ArthurLimaMiranda/Projeto_FigurePicker/Recursos/simulacao.png

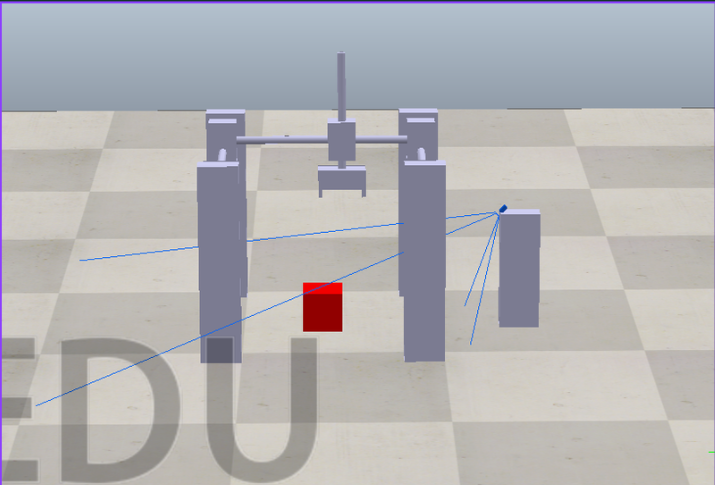
Recursos/simulacao.png
