ArthurLimaMiranda/Projeto_FigurePicker/Vision_picker/yolov11s/runs/detect/cubes_spheres_yolo11s/BoxPR_curve.png

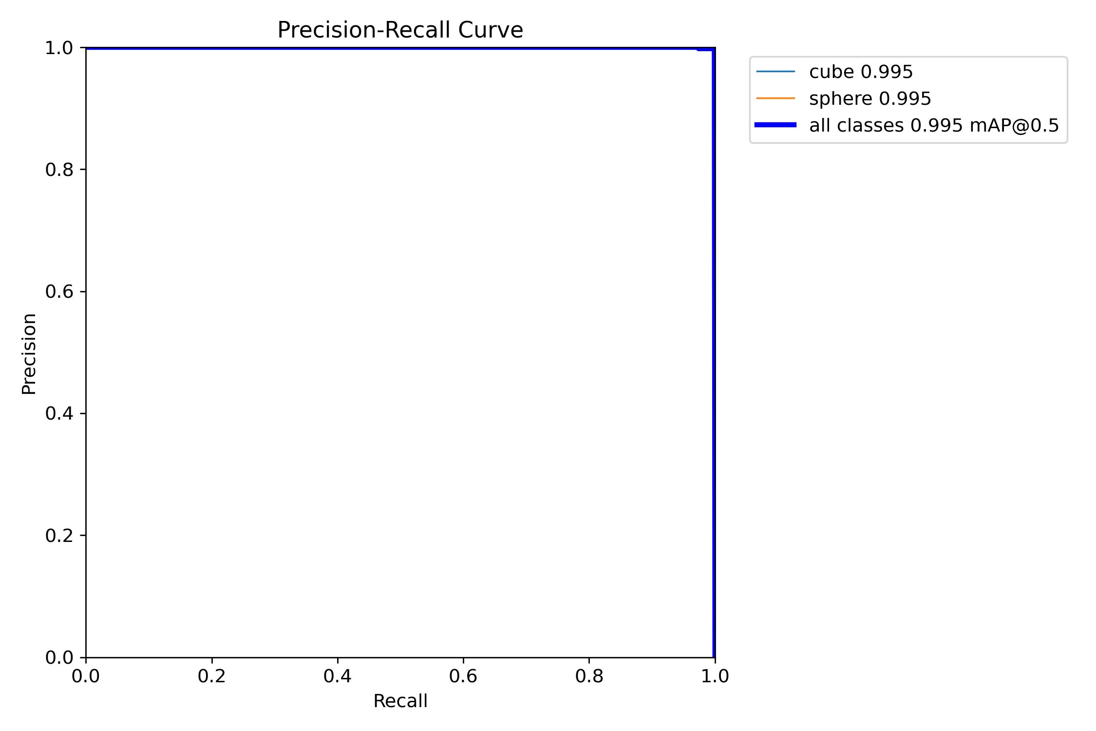
Vision_picker/yolov11s/runs/detect/cubes_spheres_yolo11s/BoxPR_curve.png
