ArthurLimaMiranda/Projeto_FigurePicker/Vision_picker/yolov11s/runs/detect/cubes_spheres_yolo11s/confusion_matrix_normalized.png

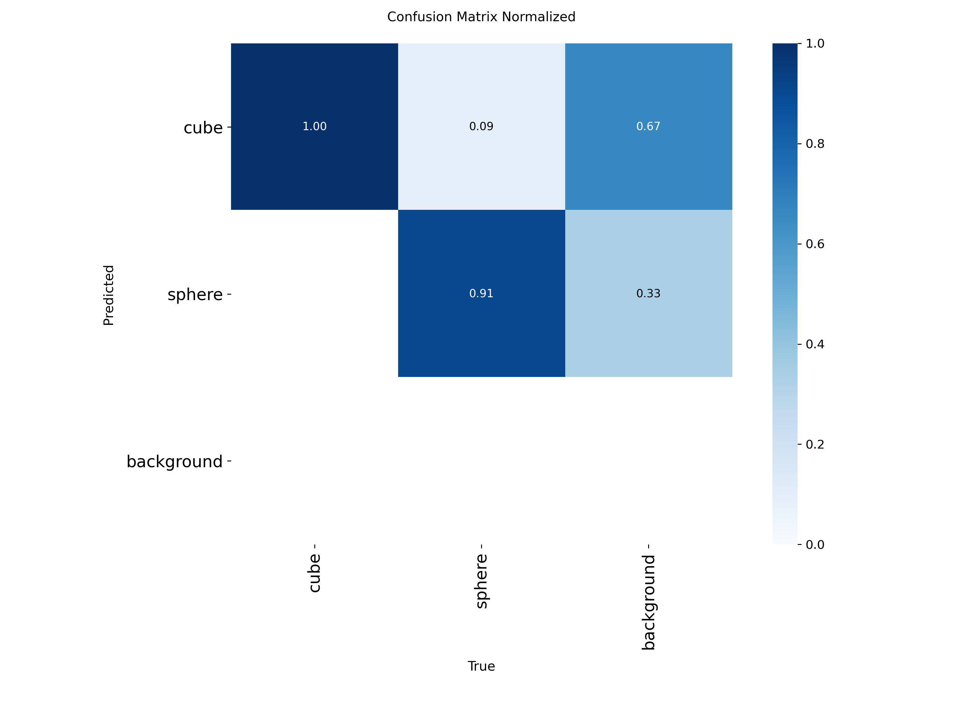
Vision_picker/yolov11s/runs/detect/cubes_spheres_yolo11s/confusion_matrix_normalized.png
