ArthurLimaMiranda/Projeto_FigurePicker/Vision_picker/yolov11s/runs/detect/cubes_spheres_yolo11s/train_batch14141.jpg

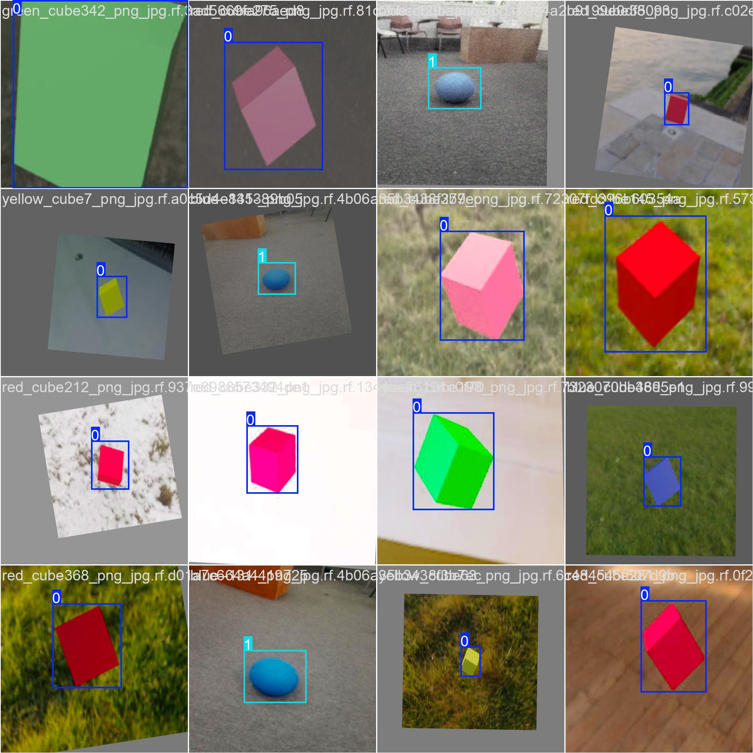
Vision_picker/yolov11s/runs/detect/cubes_spheres_yolo11s/train_batch14141.jpg
