ArthurLimaMiranda/Projeto_FigurePicker/Vision_picker/yolov11s/runs/detect/cubes_spheres_yolo11s/val_batch2_labels.jpg

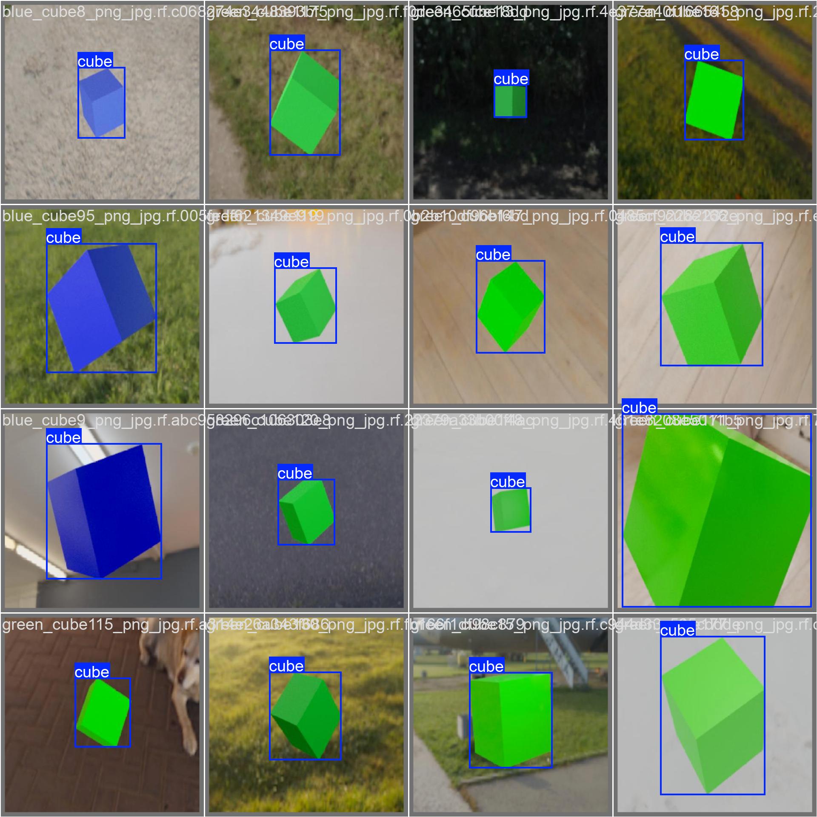
Vision_picker/yolov11s/runs/detect/cubes_spheres_yolo11s/val_batch2_labels.jpg
