ArthurLimaMiranda/Projeto_FigurePicker/Vision_picker/yolov11s/dataset_balanced/test/images/blue--84-_png_jpg.rf.567f411e10d59bb02a4530c11f7e49aa.jpg

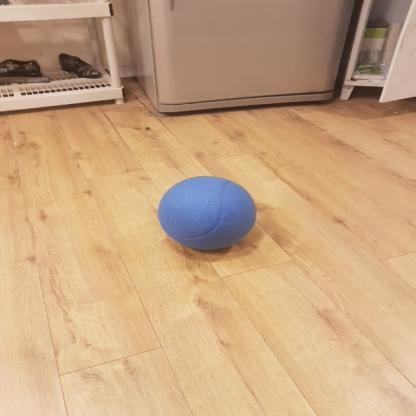
Vision_picker/yolov11s/dataset_balanced/test/images/blue--84-_png_jpg.rf.567f411e10d59bb02a4530c11f7e49aa.jpg
