ArthurLimaMiranda/Projeto_FigurePicker/Vision_picker/yolov11s/dataset_balanced/test/images/blue--93-_png_jpg.rf.6b6eae68098328bdba1f4563f4113ef7.jpg

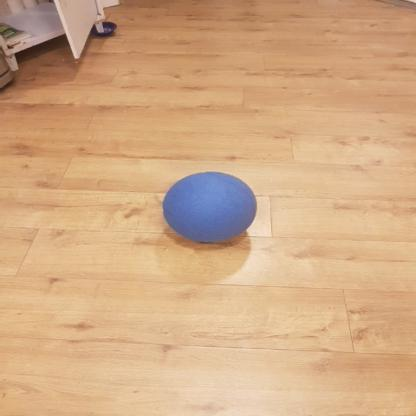
Vision_picker/yolov11s/dataset_balanced/test/images/blue--93-_png_jpg.rf.6b6eae68098328bdba1f4563f4113ef7.jpg
