ArthurLimaMiranda/Projeto_FigurePicker/Vision_picker/yolov11s/dataset_balanced/test/images/blue--100-_png_jpg.rf.dd0b86e63040361fdaaacd52fe4bce31.jpg

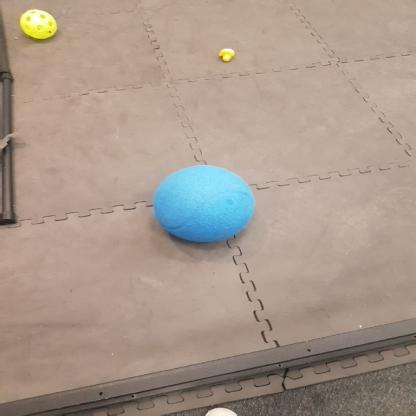
Vision_picker/yolov11s/dataset_balanced/test/images/blue--100-_png_jpg.rf.dd0b86e63040361fdaaacd52fe4bce31.jpg
