ArthurLimaMiranda/Projeto_FigurePicker/Vision_picker/yolov11s/dataset_balanced/test/images/blue_cube42_png_jpg.rf.abce69a664ab6f5cebc19ef82301c86c.jpg

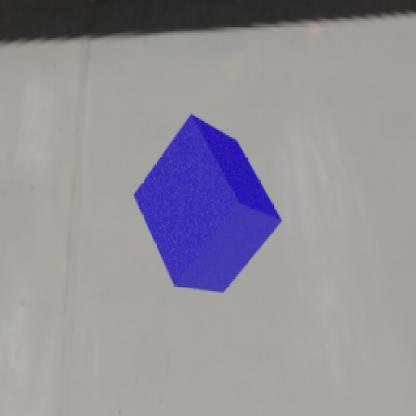
Vision_picker/yolov11s/dataset_balanced/test/images/blue_cube42_png_jpg.rf.abce69a664ab6f5cebc19ef82301c86c.jpg
