ArthurLimaMiranda/Projeto_FigurePicker/Vision_picker/yolov11s/dataset_balanced/test/images/blue_cube58_png_jpg.rf.53a362439758e62a2edbe77619f49d31.jpg

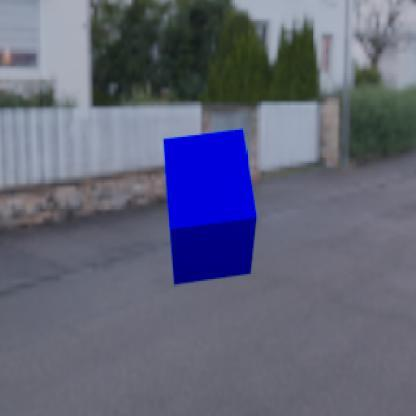
Vision_picker/yolov11s/dataset_balanced/test/images/blue_cube58_png_jpg.rf.53a362439758e62a2edbe77619f49d31.jpg
