ArthurLimaMiranda/Projeto_FigurePicker/Vision_picker/yolov11s/dataset_balanced/test/images/blue_cube85_png_jpg.rf.f3a1650c1c1776d2e01093200efaac4e.jpg

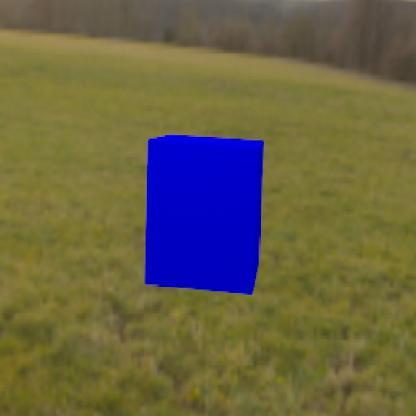
Vision_picker/yolov11s/dataset_balanced/test/images/blue_cube85_png_jpg.rf.f3a1650c1c1776d2e01093200efaac4e.jpg
