ArthurLimaMiranda/Projeto_FigurePicker/Vision_picker/yolov11s/dataset_balanced/test/images/blue_cube103_png_jpg.rf.4e462e84350769a530bda1f3ba2a9905.jpg

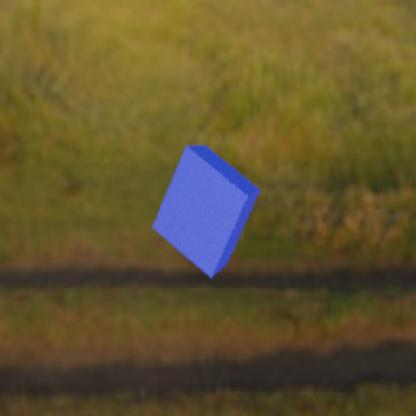
Vision_picker/yolov11s/dataset_balanced/test/images/blue_cube103_png_jpg.rf.4e462e84350769a530bda1f3ba2a9905.jpg
