ArthurLimaMiranda/Projeto_FigurePicker/Vision_picker/yolov11s/dataset_balanced/test/images/blue_cube160_png_jpg.rf.a1abcd2abb369dd8cf45045a25f46531.jpg

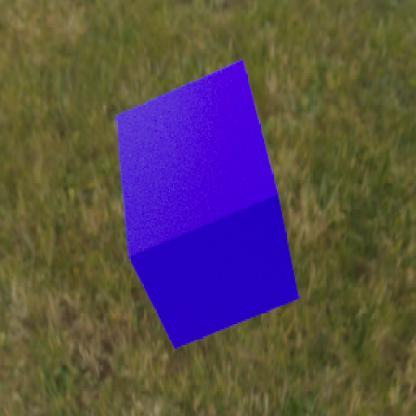
Vision_picker/yolov11s/dataset_balanced/test/images/blue_cube160_png_jpg.rf.a1abcd2abb369dd8cf45045a25f46531.jpg
