ArthurLimaMiranda/Projeto_FigurePicker/Vision_picker/yolov11s/dataset_balanced/test/images/blue_cube161_png_jpg.rf.b45ab2bd1b514e909079901d2c2f8d05.jpg

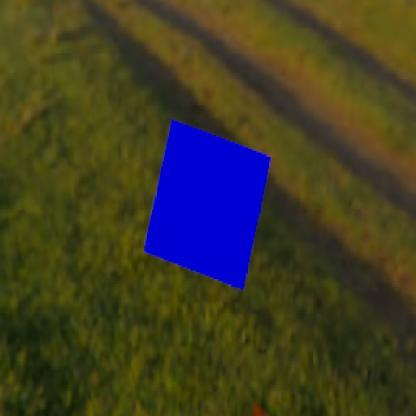
Vision_picker/yolov11s/dataset_balanced/test/images/blue_cube161_png_jpg.rf.b45ab2bd1b514e909079901d2c2f8d05.jpg
