ArthurLimaMiranda/Projeto_FigurePicker/Vision_picker/yolov11s/dataset_balanced/test/images/blue_cube162_png_jpg.rf.7f456c51b7fc784015e66de1449ef7b1.jpg

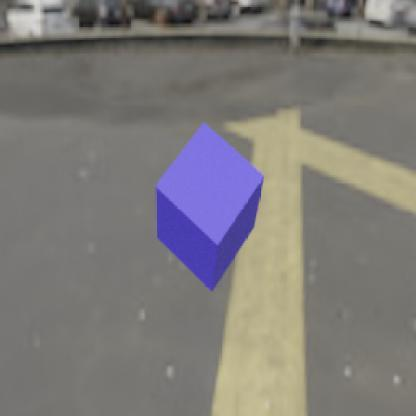
Vision_picker/yolov11s/dataset_balanced/test/images/blue_cube162_png_jpg.rf.7f456c51b7fc784015e66de1449ef7b1.jpg
