ArthurLimaMiranda/Projeto_FigurePicker/Vision_picker/yolov11s/dataset_balanced/test/images/blue_cube164_png_jpg.rf.93ee5708fcd1b85f4df0b555553770b9.jpg

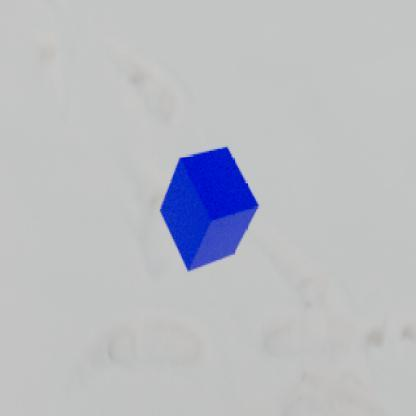
Vision_picker/yolov11s/dataset_balanced/test/images/blue_cube164_png_jpg.rf.93ee5708fcd1b85f4df0b555553770b9.jpg
