ArthurLimaMiranda/Projeto_FigurePicker/Vision_picker/yolov11s/dataset_balanced/test/images/blue_cube172_png_jpg.rf.6cf144cd701f2c703127377711581dce.jpg

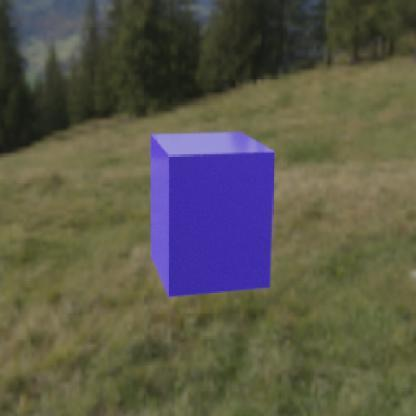
Vision_picker/yolov11s/dataset_balanced/test/images/blue_cube172_png_jpg.rf.6cf144cd701f2c703127377711581dce.jpg
