ArthurLimaMiranda/Projeto_FigurePicker/Vision_picker/yolov11s/dataset_balanced/test/images/blue_cube181_png_jpg.rf.db9952386ef1379b90a1e888cf735b6d.jpg

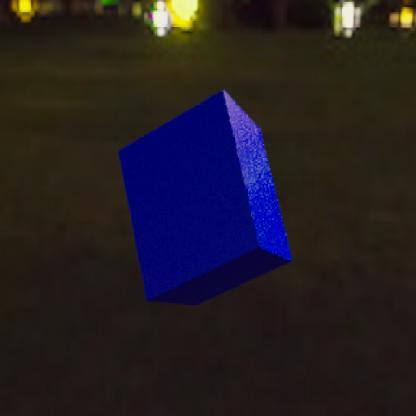
Vision_picker/yolov11s/dataset_balanced/test/images/blue_cube181_png_jpg.rf.db9952386ef1379b90a1e888cf735b6d.jpg
