ArthurLimaMiranda/Projeto_FigurePicker/Vision_picker/yolov11s/dataset_balanced/test/images/blue_cube192_png_jpg.rf.9a24825aa80906db37da28edd0c0d7d1.jpg

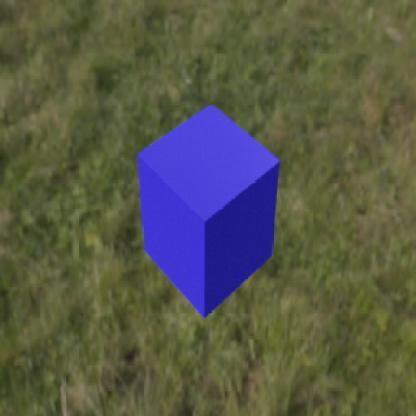
Vision_picker/yolov11s/dataset_balanced/test/images/blue_cube192_png_jpg.rf.9a24825aa80906db37da28edd0c0d7d1.jpg
