ArthurLimaMiranda/Projeto_FigurePicker/Vision_picker/yolov11s/dataset_balanced/test/images/blue_cube199_png_jpg.rf.feaa9f0d46f41d7b83ad4add980b5380.jpg

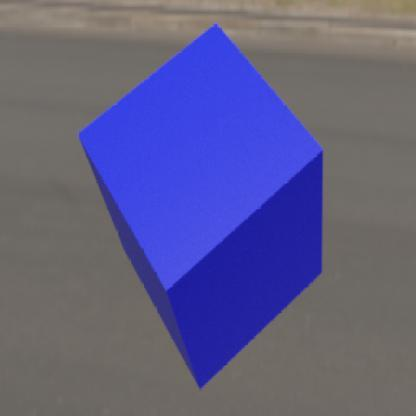
Vision_picker/yolov11s/dataset_balanced/test/images/blue_cube199_png_jpg.rf.feaa9f0d46f41d7b83ad4add980b5380.jpg
