ArthurLimaMiranda/Projeto_FigurePicker/Vision_picker/yolov11s/dataset_balanced/test/images/blue_cube204_png_jpg.rf.2f1c52ef951e825627d2c2c28c3dbf33.jpg

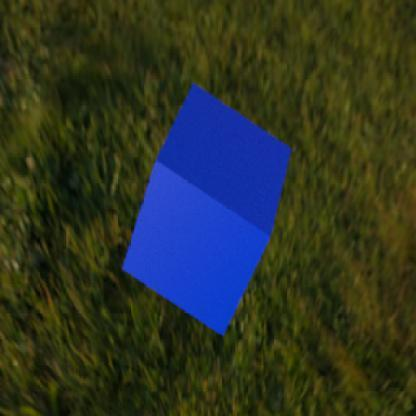
Vision_picker/yolov11s/dataset_balanced/test/images/blue_cube204_png_jpg.rf.2f1c52ef951e825627d2c2c28c3dbf33.jpg
