ArthurLimaMiranda/Projeto_FigurePicker/Vision_picker/yolov11s/dataset_balanced/test/images/blue_cube213_png_jpg.rf.dd36270e35e26b618463bcae429f0894.jpg

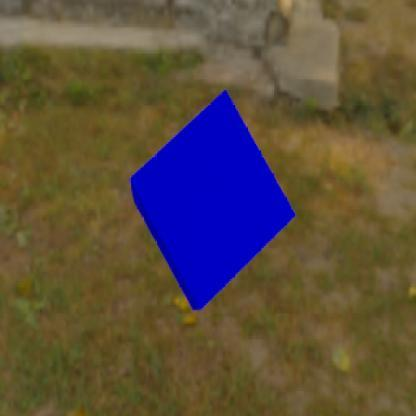
Vision_picker/yolov11s/dataset_balanced/test/images/blue_cube213_png_jpg.rf.dd36270e35e26b618463bcae429f0894.jpg
