ArthurLimaMiranda/Projeto_FigurePicker/Vision_picker/yolov11s/dataset_balanced/test/images/blue_cube215_png_jpg.rf.6778af7dd08edcb0a35833dbf11b05d6.jpg

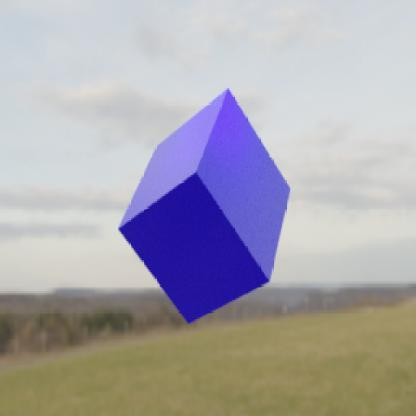
Vision_picker/yolov11s/dataset_balanced/test/images/blue_cube215_png_jpg.rf.6778af7dd08edcb0a35833dbf11b05d6.jpg
