ArthurLimaMiranda/Projeto_FigurePicker/Vision_picker/yolov11s/dataset_balanced/test/images/blue_cube231_png_jpg.rf.91c44d4d763334b19d77680f1fb3da6a.jpg

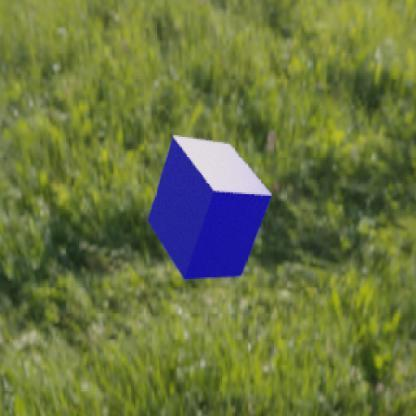
Vision_picker/yolov11s/dataset_balanced/test/images/blue_cube231_png_jpg.rf.91c44d4d763334b19d77680f1fb3da6a.jpg
