ArthurLimaMiranda/Projeto_FigurePicker/Vision_picker/yolov11s/dataset_balanced/test/images/blue_cube269_png_jpg.rf.89228ccbb0b1a1cb1eaefc8cd786519d.jpg

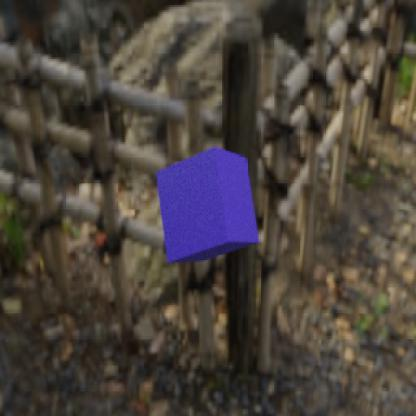
Vision_picker/yolov11s/dataset_balanced/test/images/blue_cube269_png_jpg.rf.89228ccbb0b1a1cb1eaefc8cd786519d.jpg
