ArthurLimaMiranda/Projeto_FigurePicker/Vision_picker/yolov11s/dataset_balanced/test/images/blue_cube296_png_jpg.rf.a0a6efcd4c395f7b1f52d5c792a3dc58.jpg

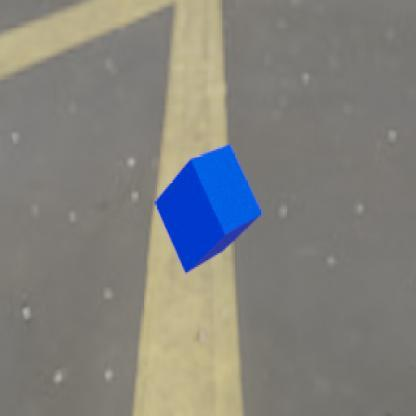
Vision_picker/yolov11s/dataset_balanced/test/images/blue_cube296_png_jpg.rf.a0a6efcd4c395f7b1f52d5c792a3dc58.jpg
