ArthurLimaMiranda/Projeto_FigurePicker/Vision_picker/yolov11s/dataset_balanced/test/images/blue_cube310_png_jpg.rf.18883e9e78c07162a2c54a4ae9cc00de.jpg

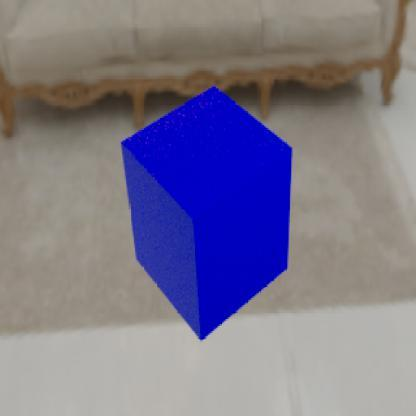
Vision_picker/yolov11s/dataset_balanced/test/images/blue_cube310_png_jpg.rf.18883e9e78c07162a2c54a4ae9cc00de.jpg
