ArthurLimaMiranda/Projeto_FigurePicker/Vision_picker/yolov11s/dataset_balanced/test/images/blue_cube329_png_jpg.rf.17cf98376a882969f6fd8f5a84324c06.jpg

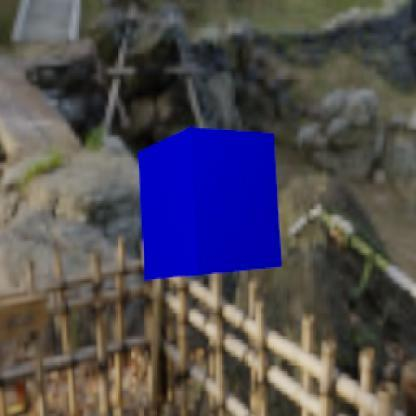
Vision_picker/yolov11s/dataset_balanced/test/images/blue_cube329_png_jpg.rf.17cf98376a882969f6fd8f5a84324c06.jpg
