ArthurLimaMiranda/Projeto_FigurePicker/Vision_picker/yolov11s/dataset_balanced/test/images/blue_cube333_png_jpg.rf.893f67814ab9e42be47a5e41bffe1e09.jpg

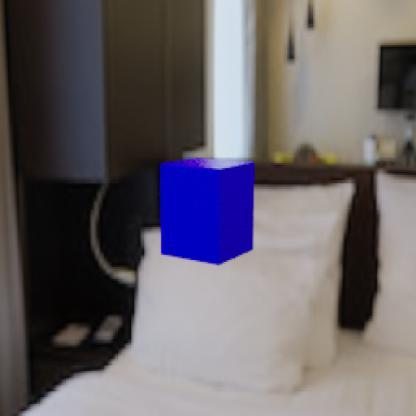
Vision_picker/yolov11s/dataset_balanced/test/images/blue_cube333_png_jpg.rf.893f67814ab9e42be47a5e41bffe1e09.jpg
