ArthurLimaMiranda/Projeto_FigurePicker/Vision_picker/yolov11s/dataset_balanced/test/images/blue_cube367_png_jpg.rf.c6c18c14dced440cc41cb3e22b2560b9.jpg

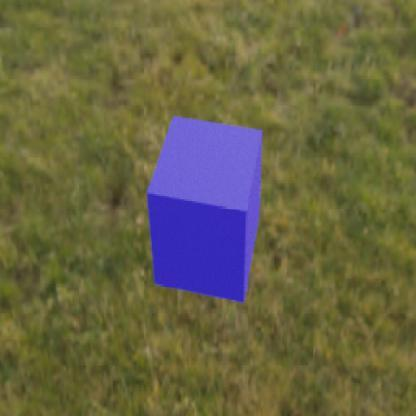
Vision_picker/yolov11s/dataset_balanced/test/images/blue_cube367_png_jpg.rf.c6c18c14dced440cc41cb3e22b2560b9.jpg
