ArthurLimaMiranda/Projeto_FigurePicker/Vision_picker/yolov11s/dataset_balanced/test/images/blue_cube368_png_jpg.rf.a7e753cfbdd82aae176ec13c49448d98.jpg

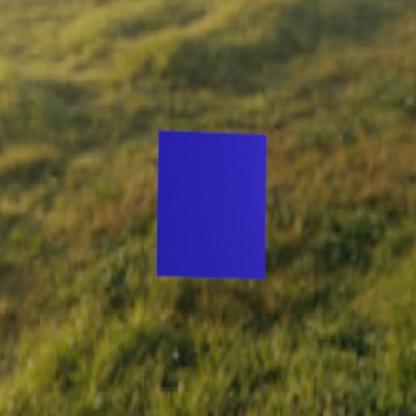
Vision_picker/yolov11s/dataset_balanced/test/images/blue_cube368_png_jpg.rf.a7e753cfbdd82aae176ec13c49448d98.jpg
