ArthurLimaMiranda/Projeto_FigurePicker/Vision_picker/yolov11s/dataset_balanced/test/images/blue_cube372_png_jpg.rf.cd5a1481575102ebce740c9146e255aa.jpg

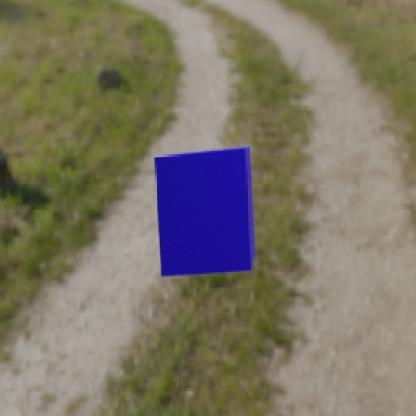
Vision_picker/yolov11s/dataset_balanced/test/images/blue_cube372_png_jpg.rf.cd5a1481575102ebce740c9146e255aa.jpg
