ArthurLimaMiranda/Projeto_FigurePicker/Vision_picker/yolov11s/dataset_balanced/test/images/blue_cube373_png_jpg.rf.ae21d8ad34c4659028b0b2ec7988f518.jpg

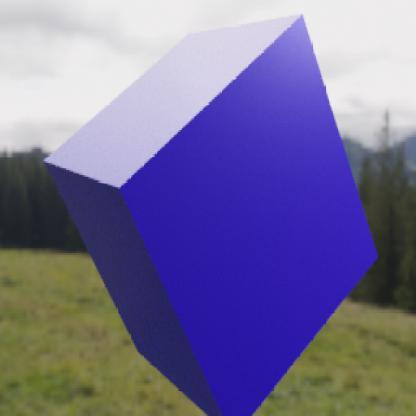
Vision_picker/yolov11s/dataset_balanced/test/images/blue_cube373_png_jpg.rf.ae21d8ad34c4659028b0b2ec7988f518.jpg
