ArthurLimaMiranda/Projeto_FigurePicker/Vision_picker/yolov11s/dataset_balanced/test/images/blue_cube379_png_jpg.rf.120e50c02136f08a4657170cf414bbbe.jpg

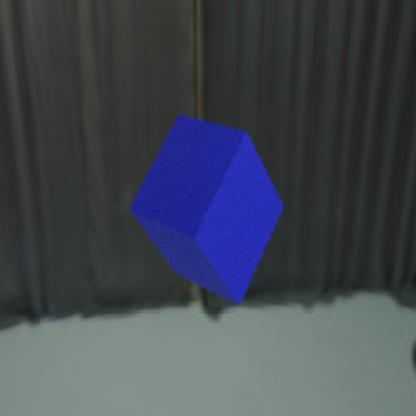
Vision_picker/yolov11s/dataset_balanced/test/images/blue_cube379_png_jpg.rf.120e50c02136f08a4657170cf414bbbe.jpg
