ArthurLimaMiranda/Projeto_FigurePicker/Vision_picker/yolov11s/dataset_balanced/test/images/green_cube21_png_jpg.rf.5a48e1e8dc54fd5de01652c4830b1c1b.jpg

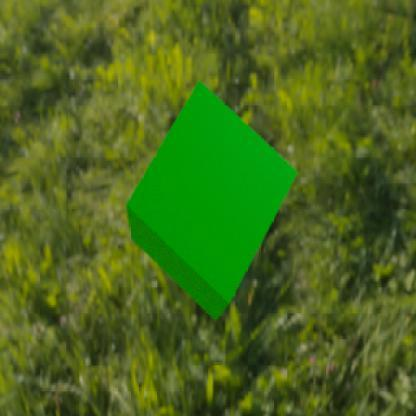
Vision_picker/yolov11s/dataset_balanced/test/images/green_cube21_png_jpg.rf.5a48e1e8dc54fd5de01652c4830b1c1b.jpg
