ArthurLimaMiranda/Projeto_FigurePicker/Vision_picker/yolov11s/dataset_balanced/test/images/green_cube22_png_jpg.rf.d32e6d478128e3506b78b1b6bc8314cc.jpg

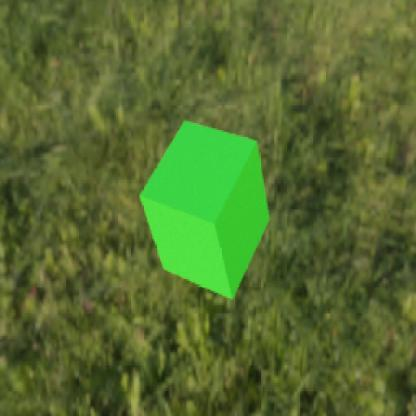
Vision_picker/yolov11s/dataset_balanced/test/images/green_cube22_png_jpg.rf.d32e6d478128e3506b78b1b6bc8314cc.jpg
