ArthurLimaMiranda/Projeto_FigurePicker/Vision_picker/yolov11s/dataset_balanced/test/images/green_cube39_png_jpg.rf.af55b9dceeb5eb2e2b9d8994aa7bebf3.jpg

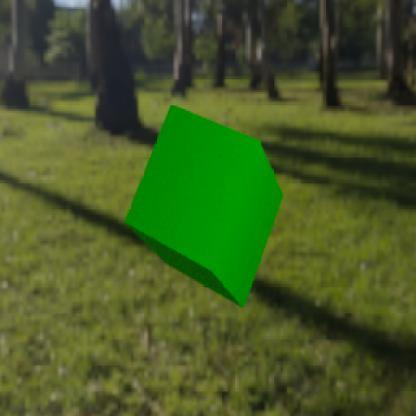
Vision_picker/yolov11s/dataset_balanced/test/images/green_cube39_png_jpg.rf.af55b9dceeb5eb2e2b9d8994aa7bebf3.jpg
