ArthurLimaMiranda/Projeto_FigurePicker/Vision_picker/yolov11s/dataset_balanced/test/images/green_cube53_png_jpg.rf.a543365e071e4346e3cd8564a33cd9c9.jpg

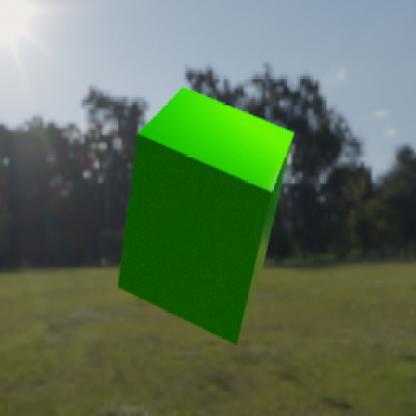
Vision_picker/yolov11s/dataset_balanced/test/images/green_cube53_png_jpg.rf.a543365e071e4346e3cd8564a33cd9c9.jpg
