ArthurLimaMiranda/Projeto_FigurePicker/Vision_picker/yolov11s/dataset_balanced/test/images/green_cube75_png_jpg.rf.1e8654ca23eda952ccb7fdbc83bcfcc3.jpg

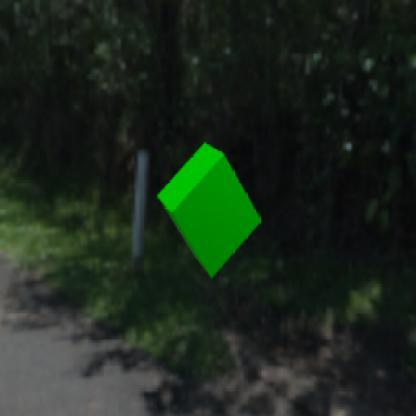
Vision_picker/yolov11s/dataset_balanced/test/images/green_cube75_png_jpg.rf.1e8654ca23eda952ccb7fdbc83bcfcc3.jpg
