ArthurLimaMiranda/Projeto_FigurePicker/Vision_picker/yolov11s/dataset_balanced/test/images/green_cube77_png_jpg.rf.02ce15547fde0a28846c3f82a8999278.jpg

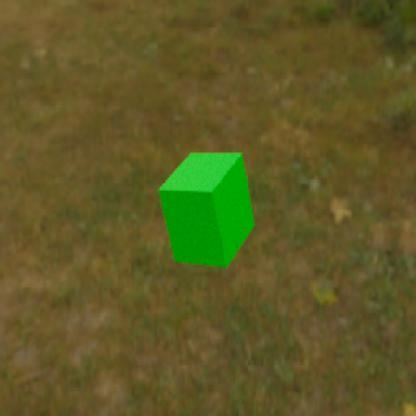
Vision_picker/yolov11s/dataset_balanced/test/images/green_cube77_png_jpg.rf.02ce15547fde0a28846c3f82a8999278.jpg
