ArthurLimaMiranda/Projeto_FigurePicker/Vision_picker/yolov11s/dataset_balanced/test/images/green_cube100_png_jpg.rf.c7b6cd9854afd8f1e6e931121f36c202.jpg

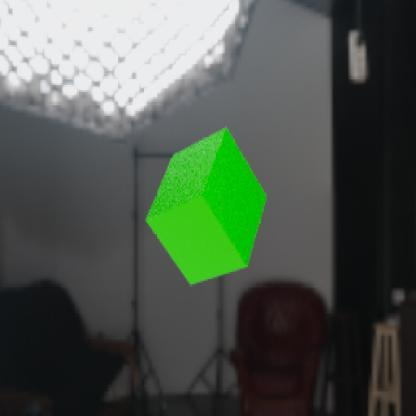
Vision_picker/yolov11s/dataset_balanced/test/images/green_cube100_png_jpg.rf.c7b6cd9854afd8f1e6e931121f36c202.jpg
