ArthurLimaMiranda/Projeto_FigurePicker/Vision_picker/yolov11s/dataset_balanced/test/images/green_cube141_png_jpg.rf.92b012205250f107fb2f7d4fdc4a4935.jpg

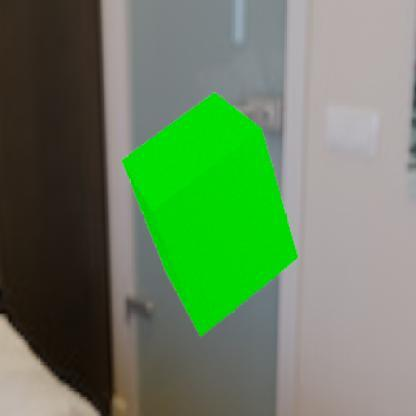
Vision_picker/yolov11s/dataset_balanced/test/images/green_cube141_png_jpg.rf.92b012205250f107fb2f7d4fdc4a4935.jpg
