ArthurLimaMiranda/Projeto_FigurePicker/Vision_picker/yolov11s/dataset_balanced/test/images/green_cube149_png_jpg.rf.b5127a95c5955a14a369f1813719cf44.jpg

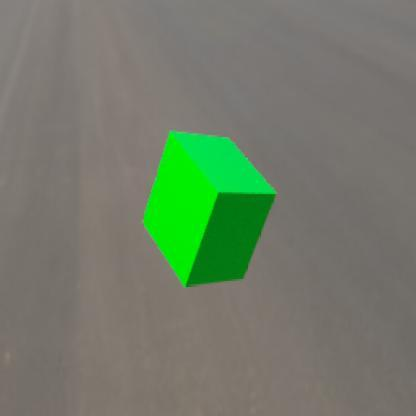
Vision_picker/yolov11s/dataset_balanced/test/images/green_cube149_png_jpg.rf.b5127a95c5955a14a369f1813719cf44.jpg
