ArthurLimaMiranda/Projeto_FigurePicker/Vision_picker/yolov11s/dataset_balanced/test/images/green_cube156_png_jpg.rf.cc39b57217f8777b7c034d6c792f9cc4.jpg

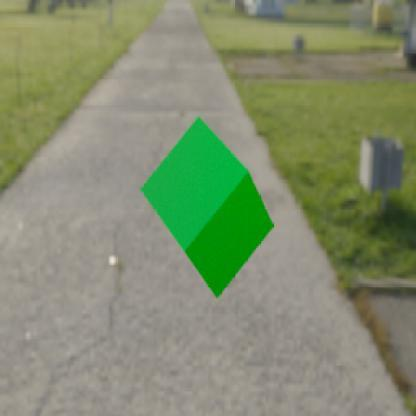
Vision_picker/yolov11s/dataset_balanced/test/images/green_cube156_png_jpg.rf.cc39b57217f8777b7c034d6c792f9cc4.jpg
