ArthurLimaMiranda/Projeto_FigurePicker/Vision_picker/yolov11s/dataset_balanced/test/images/green_cube186_png_jpg.rf.0f59c88701fbba5ef5b13ec5e51c180c.jpg

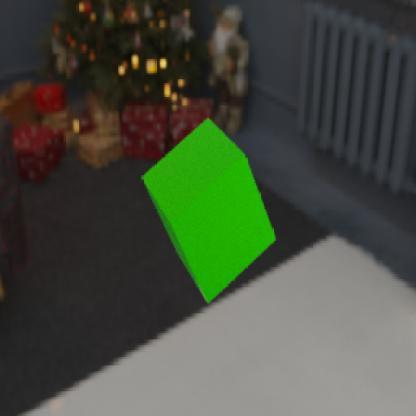
Vision_picker/yolov11s/dataset_balanced/test/images/green_cube186_png_jpg.rf.0f59c88701fbba5ef5b13ec5e51c180c.jpg
