ArthurLimaMiranda/Projeto_FigurePicker/Vision_picker/yolov11s/dataset_balanced/test/images/green_cube197_png_jpg.rf.d4bcd3aede18a281e1a44099e052ec76.jpg

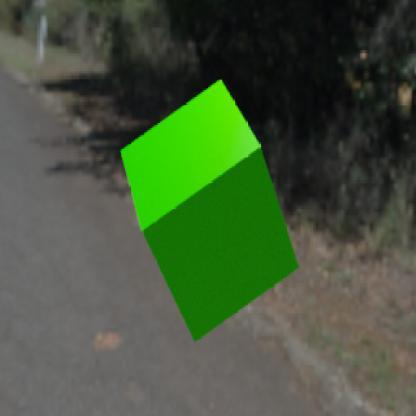
Vision_picker/yolov11s/dataset_balanced/test/images/green_cube197_png_jpg.rf.d4bcd3aede18a281e1a44099e052ec76.jpg
