ArthurLimaMiranda/Projeto_FigurePicker/Vision_picker/yolov11s/dataset_balanced/test/images/green_cube203_png_jpg.rf.85050ae4b77212836c7555dd60a6735c.jpg

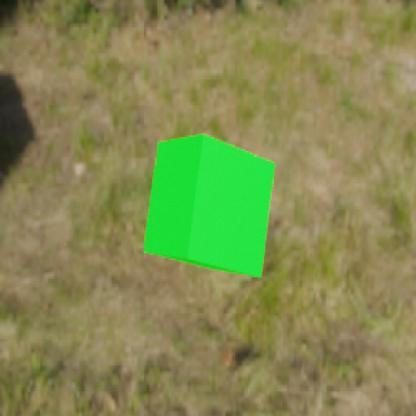
Vision_picker/yolov11s/dataset_balanced/test/images/green_cube203_png_jpg.rf.85050ae4b77212836c7555dd60a6735c.jpg
