ArthurLimaMiranda/Projeto_FigurePicker/Vision_picker/yolov11s/dataset_balanced/test/images/green_cube207_png_jpg.rf.554937a4a28a490e7348cfcd097287f5.jpg

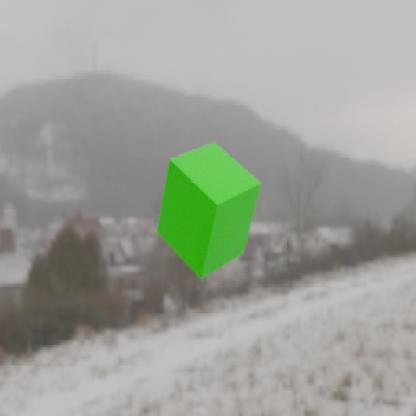
Vision_picker/yolov11s/dataset_balanced/test/images/green_cube207_png_jpg.rf.554937a4a28a490e7348cfcd097287f5.jpg
