ArthurLimaMiranda/Projeto_FigurePicker/Vision_picker/yolov11s/dataset_balanced/test/images/green_cube209_png_jpg.rf.3333e32396146f0071d544fa2a649eda.jpg

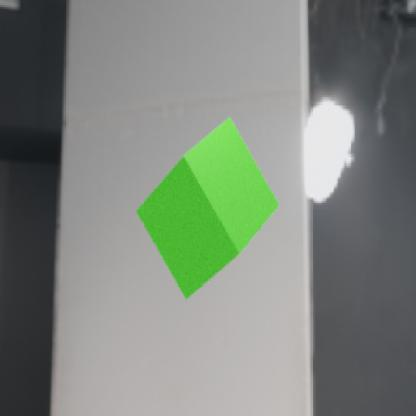
Vision_picker/yolov11s/dataset_balanced/test/images/green_cube209_png_jpg.rf.3333e32396146f0071d544fa2a649eda.jpg
