ArthurLimaMiranda/Projeto_FigurePicker/Vision_picker/yolov11s/dataset_balanced/test/images/green_cube245_png_jpg.rf.ede81e3d9919e2af759a8148c62ee3e1.jpg

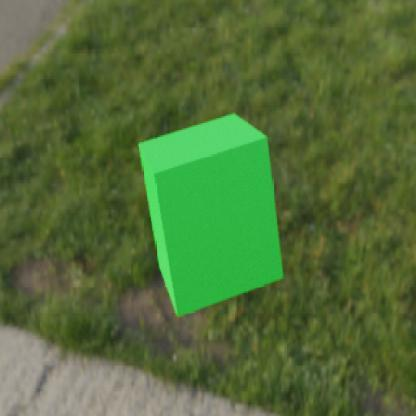
Vision_picker/yolov11s/dataset_balanced/test/images/green_cube245_png_jpg.rf.ede81e3d9919e2af759a8148c62ee3e1.jpg
