ArthurLimaMiranda/Projeto_FigurePicker/Vision_picker/yolov11s/dataset_balanced/test/images/green_cube248_png_jpg.rf.629ede3b3348e954eb9f17b2891f2111.jpg

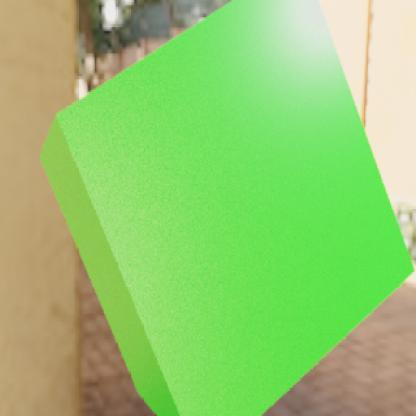
Vision_picker/yolov11s/dataset_balanced/test/images/green_cube248_png_jpg.rf.629ede3b3348e954eb9f17b2891f2111.jpg
