ArthurLimaMiranda/Projeto_FigurePicker/Vision_picker/yolov11s/dataset_balanced/test/images/green_cube259_png_jpg.rf.6f941f1306cee4b02812a302f71bff45.jpg

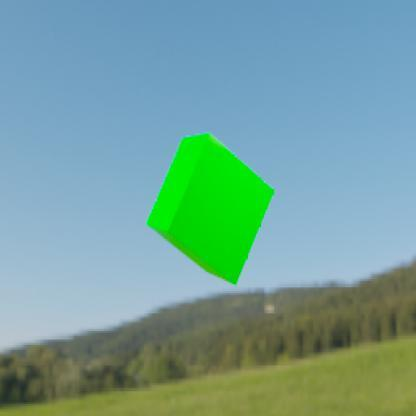
Vision_picker/yolov11s/dataset_balanced/test/images/green_cube259_png_jpg.rf.6f941f1306cee4b02812a302f71bff45.jpg
