ArthurLimaMiranda/Projeto_FigurePicker/Vision_picker/yolov11s/dataset_balanced/test/images/green_cube261_png_jpg.rf.72f2ab91f44654ba2b3f1ae77ee24397.jpg

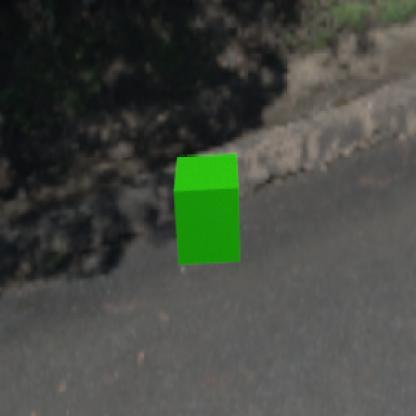
Vision_picker/yolov11s/dataset_balanced/test/images/green_cube261_png_jpg.rf.72f2ab91f44654ba2b3f1ae77ee24397.jpg
