ArthurLimaMiranda/Projeto_FigurePicker/Vision_picker/yolov11s/dataset_balanced/test/images/green_cube313_png_jpg.rf.c6db6e5af662e48ced9c6490a1e5cef0.jpg

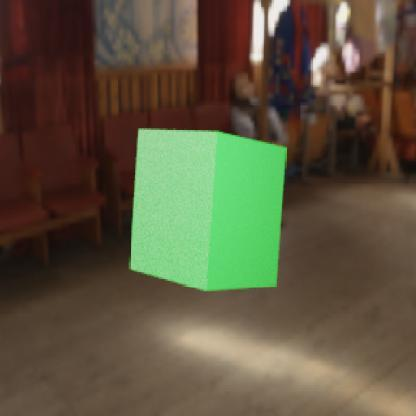
Vision_picker/yolov11s/dataset_balanced/test/images/green_cube313_png_jpg.rf.c6db6e5af662e48ced9c6490a1e5cef0.jpg
