ArthurLimaMiranda/Projeto_FigurePicker/Vision_picker/yolov11s/dataset_balanced/test/images/green_cube315_png_jpg.rf.b4dfe72a7dcb189ceb7465ed858d8e0b.jpg

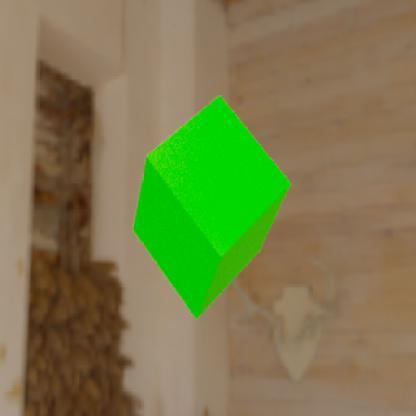
Vision_picker/yolov11s/dataset_balanced/test/images/green_cube315_png_jpg.rf.b4dfe72a7dcb189ceb7465ed858d8e0b.jpg
