ArthurLimaMiranda/Projeto_FigurePicker/Vision_picker/yolov11s/dataset_balanced/test/images/green_cube316_png_jpg.rf.7185d819912117d0decf25caf31fce8a.jpg

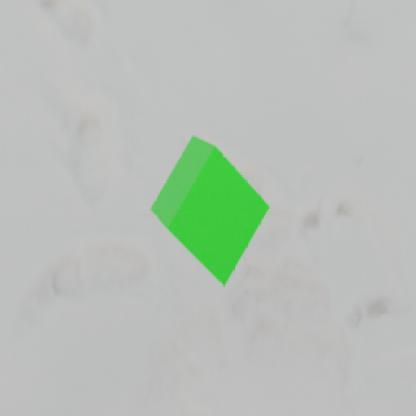
Vision_picker/yolov11s/dataset_balanced/test/images/green_cube316_png_jpg.rf.7185d819912117d0decf25caf31fce8a.jpg
