ArthurLimaMiranda/Projeto_FigurePicker/Vision_picker/yolov11s/dataset_balanced/test/images/green_cube317_png_jpg.rf.2ea56c4ea6ff85ae463b7b4873430975.jpg

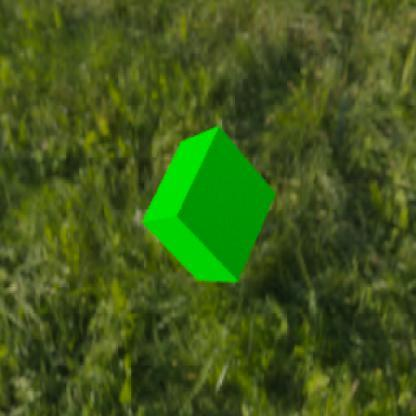
Vision_picker/yolov11s/dataset_balanced/test/images/green_cube317_png_jpg.rf.2ea56c4ea6ff85ae463b7b4873430975.jpg
