ArthurLimaMiranda/Projeto_FigurePicker/Vision_picker/yolov11s/dataset_balanced/test/images/green_cube318_png_jpg.rf.0602639b5c39f474e4a0ae10414525d9.jpg

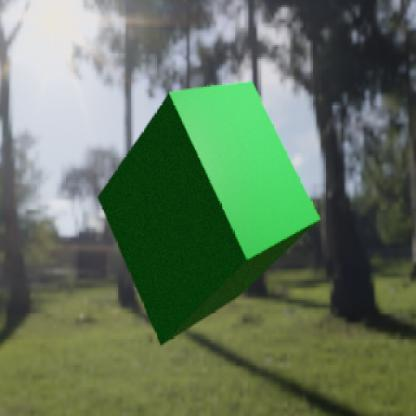
Vision_picker/yolov11s/dataset_balanced/test/images/green_cube318_png_jpg.rf.0602639b5c39f474e4a0ae10414525d9.jpg
