ArthurLimaMiranda/Projeto_FigurePicker/Vision_picker/yolov11s/dataset_balanced/test/images/green_cube330_png_jpg.rf.46c3cfd85b48fd63bd3395b83e215ee0.jpg

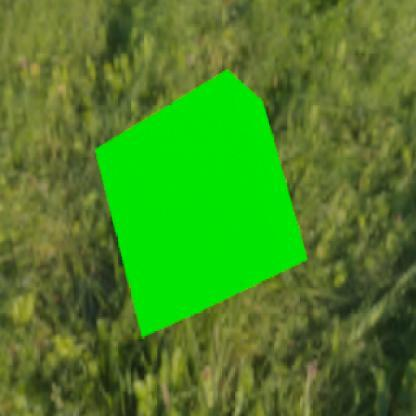
Vision_picker/yolov11s/dataset_balanced/test/images/green_cube330_png_jpg.rf.46c3cfd85b48fd63bd3395b83e215ee0.jpg
