ArthurLimaMiranda/Projeto_FigurePicker/Vision_picker/yolov11s/dataset_balanced/test/images/green_cube335_png_jpg.rf.0e59756b07e247aec925e7c8cd700504.jpg

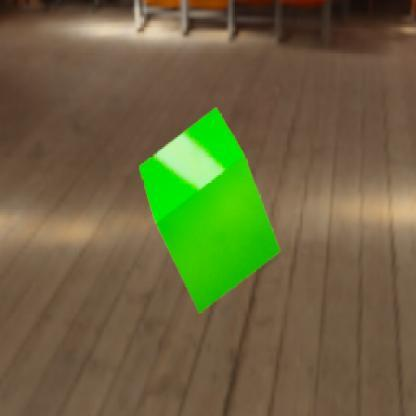
Vision_picker/yolov11s/dataset_balanced/test/images/green_cube335_png_jpg.rf.0e59756b07e247aec925e7c8cd700504.jpg
