ArthurLimaMiranda/Projeto_FigurePicker/Vision_picker/yolov11s/dataset_balanced/test/images/green_cube345_png_jpg.rf.09ca5a2508774dc8d157d9349ff66878.jpg

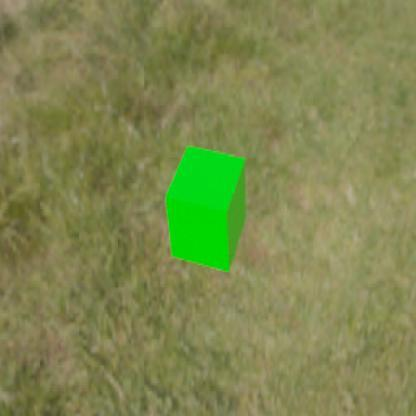
Vision_picker/yolov11s/dataset_balanced/test/images/green_cube345_png_jpg.rf.09ca5a2508774dc8d157d9349ff66878.jpg
