ArthurLimaMiranda/Projeto_FigurePicker/Vision_picker/yolov11s/dataset_balanced/test/images/green_cube354_png_jpg.rf.1cdb44712f845e15cdc1f87648f3cfe1.jpg

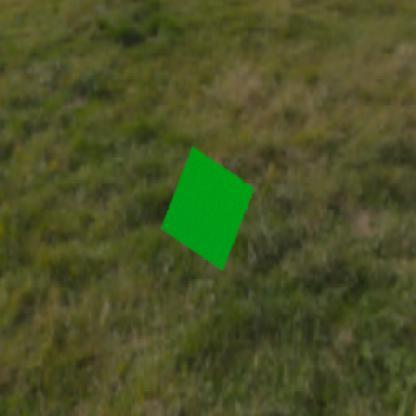
Vision_picker/yolov11s/dataset_balanced/test/images/green_cube354_png_jpg.rf.1cdb44712f845e15cdc1f87648f3cfe1.jpg
