ArthurLimaMiranda/Projeto_FigurePicker/Vision_picker/yolov11s/dataset_balanced/test/images/green_cube370_png_jpg.rf.e815c47c938266a46ba5bcc88612326e.jpg

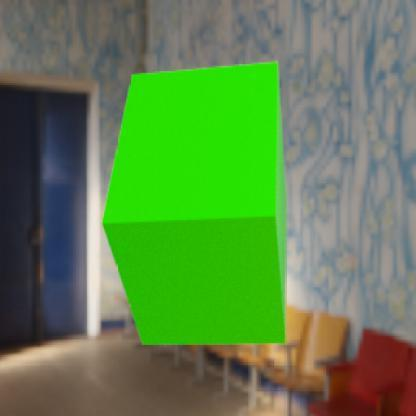
Vision_picker/yolov11s/dataset_balanced/test/images/green_cube370_png_jpg.rf.e815c47c938266a46ba5bcc88612326e.jpg
