ArthurLimaMiranda/Projeto_FigurePicker/Vision_picker/yolov11s/dataset_balanced/test/images/green_cube381_png_jpg.rf.f940a3d7d202b70b220cd426b800dc26.jpg

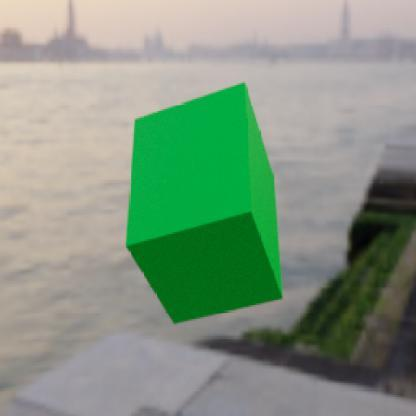
Vision_picker/yolov11s/dataset_balanced/test/images/green_cube381_png_jpg.rf.f940a3d7d202b70b220cd426b800dc26.jpg
