ArthurLimaMiranda/Projeto_FigurePicker/Vision_picker/yolov11s/dataset_balanced/test/images/red_cube1_png_jpg.rf.12a9ff4c8319fa7311066659f8cb699c.jpg

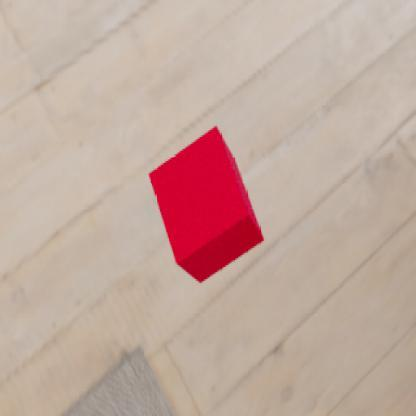
Vision_picker/yolov11s/dataset_balanced/test/images/red_cube1_png_jpg.rf.12a9ff4c8319fa7311066659f8cb699c.jpg
