ArthurLimaMiranda/Projeto_FigurePicker/Vision_picker/yolov11s/dataset_balanced/test/images/red_cube11_png_jpg.rf.52d88d9428be6d47090974cac775380f.jpg

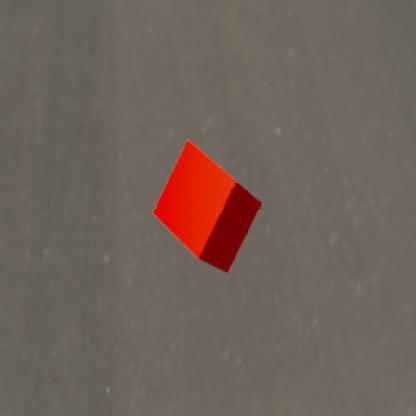
Vision_picker/yolov11s/dataset_balanced/test/images/red_cube11_png_jpg.rf.52d88d9428be6d47090974cac775380f.jpg
