ArthurLimaMiranda/Projeto_FigurePicker/Vision_picker/yolov11s/dataset_balanced/test/images/red_cube21_png_jpg.rf.ef27f31154a85d120f0ab3bdae12abf0.jpg

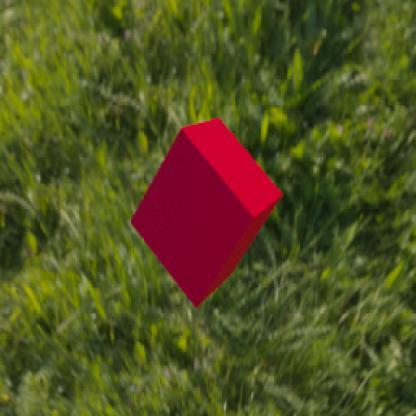
Vision_picker/yolov11s/dataset_balanced/test/images/red_cube21_png_jpg.rf.ef27f31154a85d120f0ab3bdae12abf0.jpg
