ArthurLimaMiranda/Projeto_FigurePicker/Vision_picker/yolov11s/dataset_balanced/test/images/red_cube36_png_jpg.rf.eda6bcafc20f6e10a367dd1a326477b0.jpg

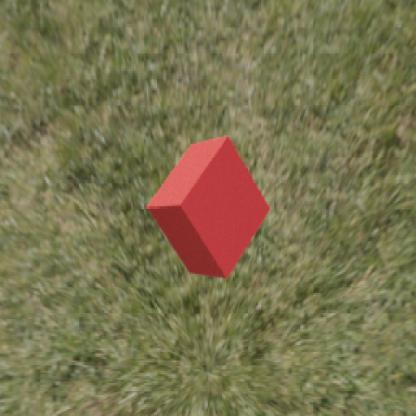
Vision_picker/yolov11s/dataset_balanced/test/images/red_cube36_png_jpg.rf.eda6bcafc20f6e10a367dd1a326477b0.jpg
