ArthurLimaMiranda/Projeto_FigurePicker/Vision_picker/yolov11s/dataset_balanced/test/images/red_cube37_png_jpg.rf.5bea3a9832ca203bd940dfd7f4df21c9.jpg

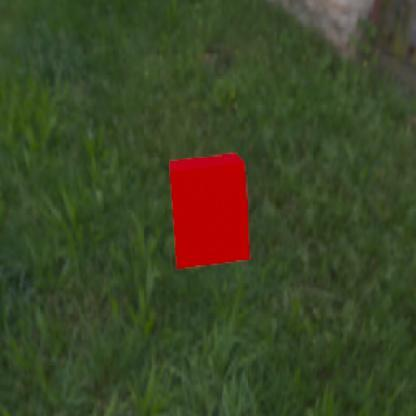
Vision_picker/yolov11s/dataset_balanced/test/images/red_cube37_png_jpg.rf.5bea3a9832ca203bd940dfd7f4df21c9.jpg
