ArthurLimaMiranda/Projeto_FigurePicker/Vision_picker/yolov11s/dataset_balanced/test/images/red_cube42_png_jpg.rf.2cb523b7be370032452fb9febcea76e4.jpg

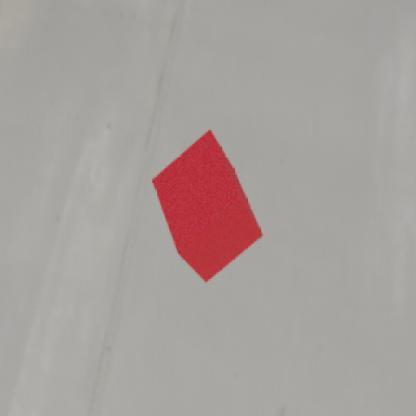
Vision_picker/yolov11s/dataset_balanced/test/images/red_cube42_png_jpg.rf.2cb523b7be370032452fb9febcea76e4.jpg
