ArthurLimaMiranda/Projeto_FigurePicker/Vision_picker/yolov11s/dataset_balanced/test/images/red_cube62_png_jpg.rf.4bcb46316ceeb9ce2738a714ec3799a5.jpg

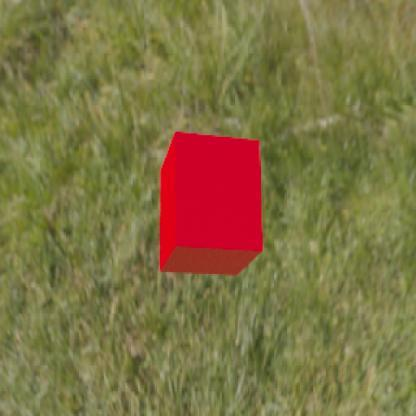
Vision_picker/yolov11s/dataset_balanced/test/images/red_cube62_png_jpg.rf.4bcb46316ceeb9ce2738a714ec3799a5.jpg
