ArthurLimaMiranda/Projeto_FigurePicker/Vision_picker/yolov11s/dataset_balanced/test/images/red_cube72_png_jpg.rf.16e69b74bbb678c6e5f5ae4e15a690e9.jpg

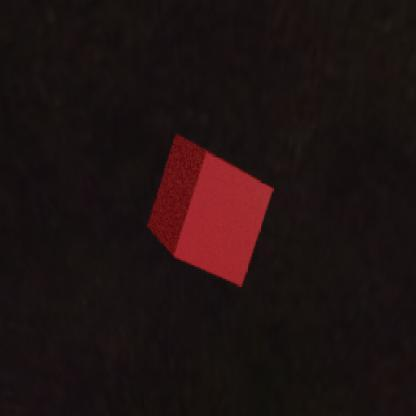
Vision_picker/yolov11s/dataset_balanced/test/images/red_cube72_png_jpg.rf.16e69b74bbb678c6e5f5ae4e15a690e9.jpg
