ArthurLimaMiranda/Projeto_FigurePicker/Vision_picker/yolov11s/dataset_balanced/test/images/red_cube77_png_jpg.rf.f59b15a69978fc991e5d5aa8f547c59b.jpg

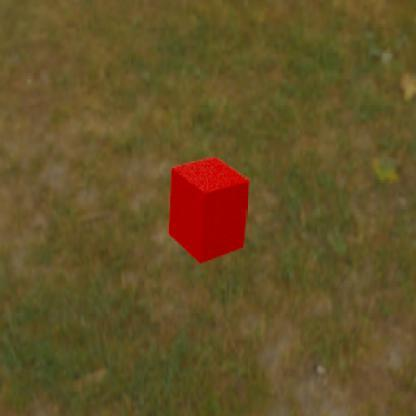
Vision_picker/yolov11s/dataset_balanced/test/images/red_cube77_png_jpg.rf.f59b15a69978fc991e5d5aa8f547c59b.jpg
