ArthurLimaMiranda/Projeto_FigurePicker/Vision_picker/yolov11s/dataset_balanced/test/images/red_cube78_png_jpg.rf.477aa60bc45b1a379865d5e556522a80.jpg

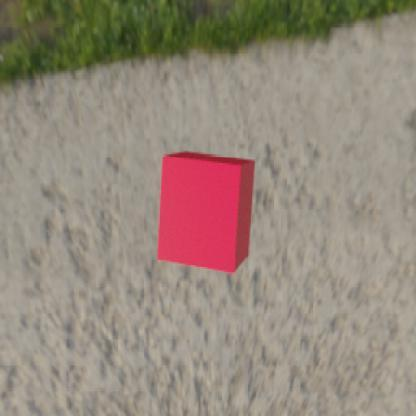
Vision_picker/yolov11s/dataset_balanced/test/images/red_cube78_png_jpg.rf.477aa60bc45b1a379865d5e556522a80.jpg
