ArthurLimaMiranda/Projeto_FigurePicker/Vision_picker/yolov11s/dataset_balanced/test/images/red_cube82_png_jpg.rf.de23254ae5bf16453b263ab9e13311e9.jpg

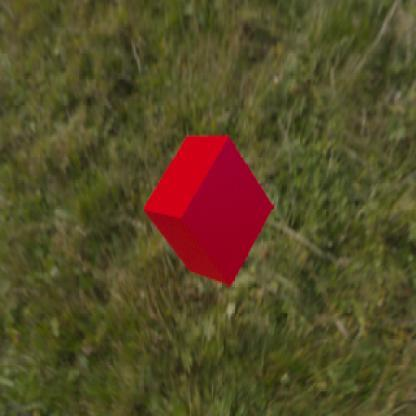
Vision_picker/yolov11s/dataset_balanced/test/images/red_cube82_png_jpg.rf.de23254ae5bf16453b263ab9e13311e9.jpg
