ArthurLimaMiranda/Projeto_FigurePicker/Vision_picker/yolov11s/dataset_balanced/test/images/red_cube88_png_jpg.rf.3d21acf35e937c2502a5a8247d9fa1c8.jpg

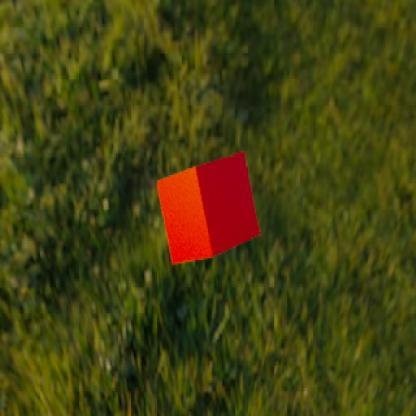
Vision_picker/yolov11s/dataset_balanced/test/images/red_cube88_png_jpg.rf.3d21acf35e937c2502a5a8247d9fa1c8.jpg
