ArthurLimaMiranda/Projeto_FigurePicker/Vision_picker/yolov11s/dataset_balanced/test/images/red_cube129_png_jpg.rf.9728a2f1c8efb23e54aa914c335af65f.jpg

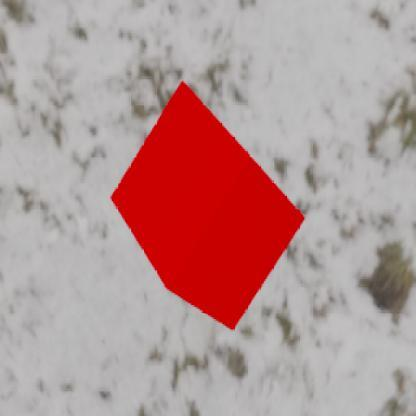
Vision_picker/yolov11s/dataset_balanced/test/images/red_cube129_png_jpg.rf.9728a2f1c8efb23e54aa914c335af65f.jpg
