ArthurLimaMiranda/Projeto_FigurePicker/Vision_picker/yolov11s/dataset_balanced/test/images/red_cube183_png_jpg.rf.2d7ab9ccfa61dd6f800fa1d20d9b65cf.jpg

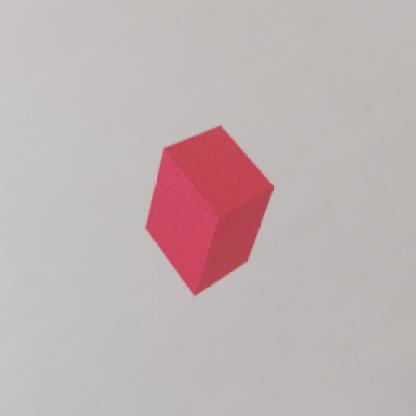
Vision_picker/yolov11s/dataset_balanced/test/images/red_cube183_png_jpg.rf.2d7ab9ccfa61dd6f800fa1d20d9b65cf.jpg
