ArthurLimaMiranda/Projeto_FigurePicker/Vision_picker/yolov11s/dataset_balanced/test/images/red_cube203_png_jpg.rf.5bb737ca3c2466e931598773f7a8b3aa.jpg

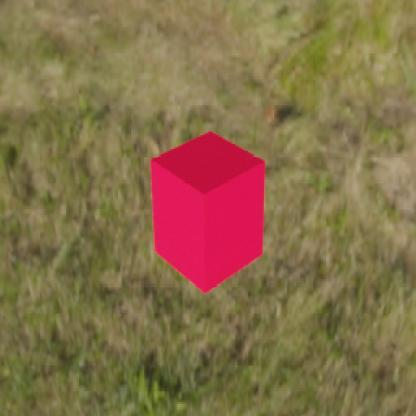
Vision_picker/yolov11s/dataset_balanced/test/images/red_cube203_png_jpg.rf.5bb737ca3c2466e931598773f7a8b3aa.jpg
