ArthurLimaMiranda/Projeto_FigurePicker/Vision_picker/yolov11s/dataset_balanced/test/images/red_cube210_png_jpg.rf.c158d5ac41cbb95fc388dd4186004c7f.jpg

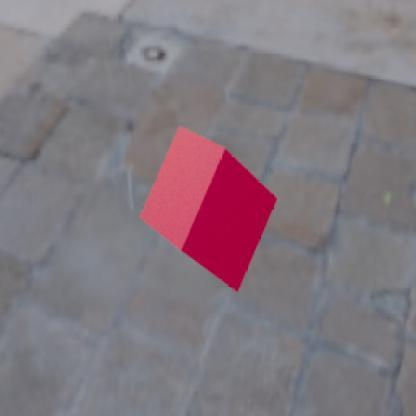
Vision_picker/yolov11s/dataset_balanced/test/images/red_cube210_png_jpg.rf.c158d5ac41cbb95fc388dd4186004c7f.jpg
