ArthurLimaMiranda/Projeto_FigurePicker/Vision_picker/yolov11s/dataset_balanced/test/images/red_cube241_png_jpg.rf.131772848f49aea171e3d8dd8b58f3ff.jpg

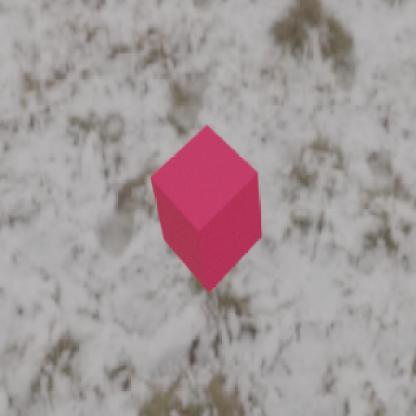
Vision_picker/yolov11s/dataset_balanced/test/images/red_cube241_png_jpg.rf.131772848f49aea171e3d8dd8b58f3ff.jpg
