ArthurLimaMiranda/Projeto_FigurePicker/Vision_picker/yolov11s/dataset_balanced/test/images/red_cube248_png_jpg.rf.0dd7258c2b151562c6b40764b809f6df.jpg

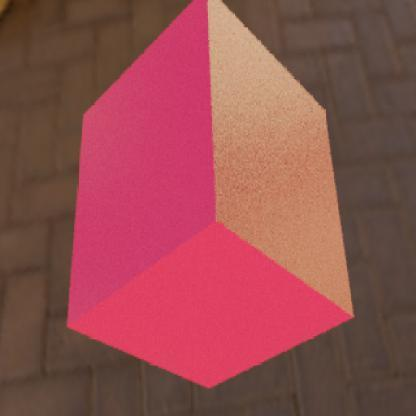
Vision_picker/yolov11s/dataset_balanced/test/images/red_cube248_png_jpg.rf.0dd7258c2b151562c6b40764b809f6df.jpg
