ArthurLimaMiranda/Projeto_FigurePicker/Vision_picker/yolov11s/dataset_balanced/test/images/red_cube291_png_jpg.rf.94ed5828f2ad3c1db7b3b5356814b94c.jpg

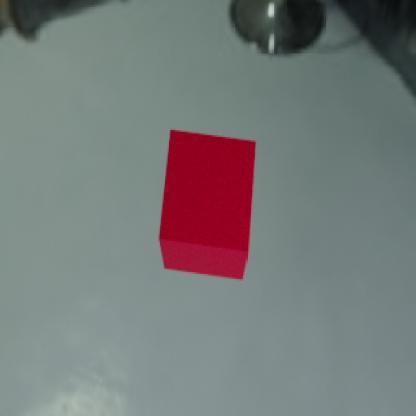
Vision_picker/yolov11s/dataset_balanced/test/images/red_cube291_png_jpg.rf.94ed5828f2ad3c1db7b3b5356814b94c.jpg
