ArthurLimaMiranda/Projeto_FigurePicker/Vision_picker/yolov11s/dataset_balanced/test/images/red_cube308_png_jpg.rf.21fc58661d30e0e6bc32384053fd78dc.jpg

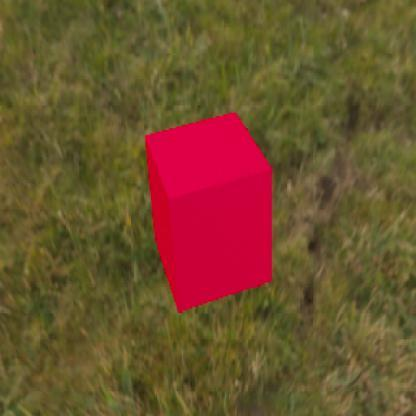
Vision_picker/yolov11s/dataset_balanced/test/images/red_cube308_png_jpg.rf.21fc58661d30e0e6bc32384053fd78dc.jpg
