ArthurLimaMiranda/Projeto_FigurePicker/Vision_picker/yolov11s/dataset_balanced/test/images/red_cube363_png_jpg.rf.90f93389ddb92f0c6514a19ade6145b0.jpg

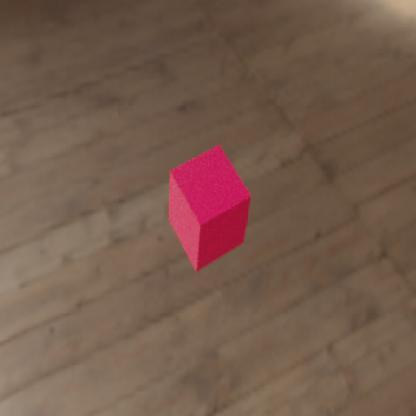
Vision_picker/yolov11s/dataset_balanced/test/images/red_cube363_png_jpg.rf.90f93389ddb92f0c6514a19ade6145b0.jpg
