ArthurLimaMiranda/Projeto_FigurePicker/Vision_picker/yolov11s/dataset_balanced/test/images/red_cube376_png_jpg.rf.913c043f7a7634f0c483ec2ccc61f34d.jpg

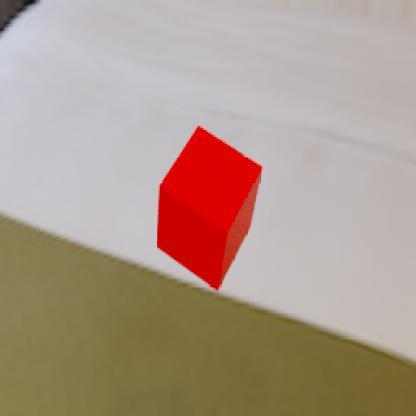
Vision_picker/yolov11s/dataset_balanced/test/images/red_cube376_png_jpg.rf.913c043f7a7634f0c483ec2ccc61f34d.jpg
