ArthurLimaMiranda/Projeto_FigurePicker/Vision_picker/yolov11s/dataset_balanced/test/images/red_cube378_png_jpg.rf.2d0f35b13396b77aebe53f2d7ccbb9f2.jpg

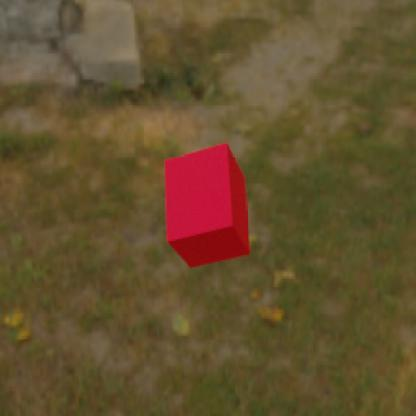
Vision_picker/yolov11s/dataset_balanced/test/images/red_cube378_png_jpg.rf.2d0f35b13396b77aebe53f2d7ccbb9f2.jpg
