ArthurLimaMiranda/Projeto_FigurePicker/Vision_picker/yolov11s/dataset_balanced/test/images/red_cube383_png_jpg.rf.9588d4728521b02fa4d33a62883bb12d.jpg

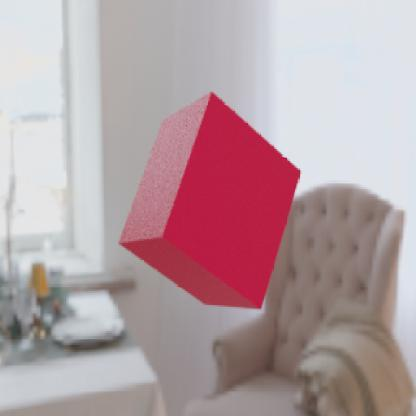
Vision_picker/yolov11s/dataset_balanced/test/images/red_cube383_png_jpg.rf.9588d4728521b02fa4d33a62883bb12d.jpg
