ArthurLimaMiranda/Projeto_FigurePicker/Vision_picker/yolov11s/dataset_balanced/test/images/red_cube385_png_jpg.rf.5a1bdecec10b52e986ff21711d4da522.jpg

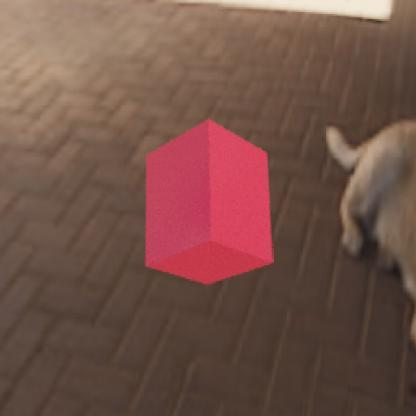
Vision_picker/yolov11s/dataset_balanced/test/images/red_cube385_png_jpg.rf.5a1bdecec10b52e986ff21711d4da522.jpg
