ArthurLimaMiranda/Projeto_FigurePicker/Vision_picker/yolov11s/dataset_balanced/test/images/yellow_cube21_png_jpg.rf.7aa079b2bf0c28a805b33d9b1158fcb8.jpg

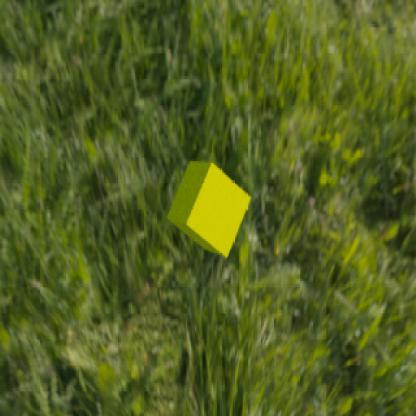
Vision_picker/yolov11s/dataset_balanced/test/images/yellow_cube21_png_jpg.rf.7aa079b2bf0c28a805b33d9b1158fcb8.jpg
