ArthurLimaMiranda/Projeto_FigurePicker/Vision_picker/yolov11s/dataset_balanced/test/images/yellow_cube23_png_jpg.rf.11a31e0cf16e01f95d5ee9e1ca3b1e31.jpg

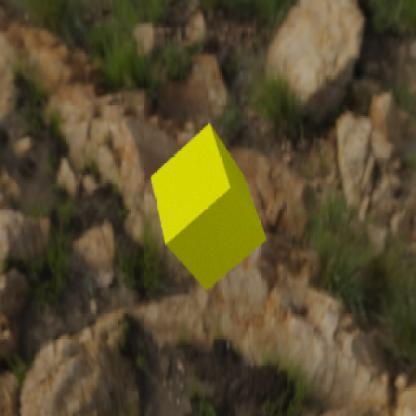
Vision_picker/yolov11s/dataset_balanced/test/images/yellow_cube23_png_jpg.rf.11a31e0cf16e01f95d5ee9e1ca3b1e31.jpg
