ArthurLimaMiranda/Projeto_FigurePicker/Vision_picker/yolov11s/dataset_balanced/test/images/yellow_cube52_png_jpg.rf.c51226206f6eb83d7ae8a258584deee1.jpg

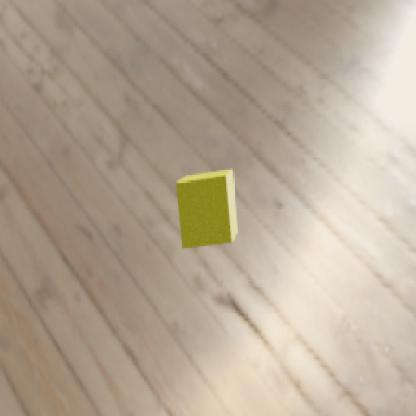
Vision_picker/yolov11s/dataset_balanced/test/images/yellow_cube52_png_jpg.rf.c51226206f6eb83d7ae8a258584deee1.jpg
