ArthurLimaMiranda/Projeto_FigurePicker/Vision_picker/yolov11s/dataset_balanced/test/images/yellow_cube54_png_jpg.rf.dd5a7b9e6d58aa211e6646e6e05f6ae4.jpg

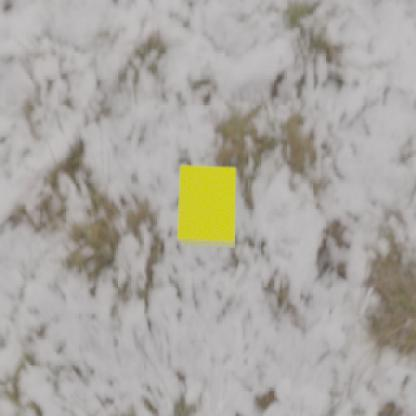
Vision_picker/yolov11s/dataset_balanced/test/images/yellow_cube54_png_jpg.rf.dd5a7b9e6d58aa211e6646e6e05f6ae4.jpg
