ArthurLimaMiranda/Projeto_FigurePicker/Vision_picker/yolov11s/dataset_balanced/test/images/yellow_cube104_png_jpg.rf.3a5912b6c89fb44bcc903d63759808ac.jpg

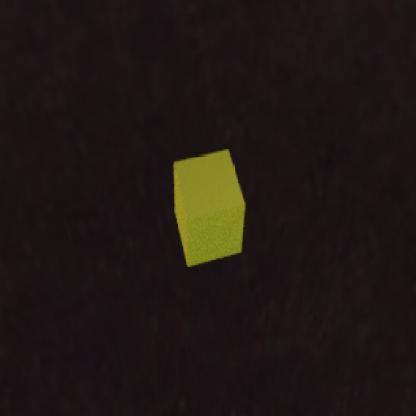
Vision_picker/yolov11s/dataset_balanced/test/images/yellow_cube104_png_jpg.rf.3a5912b6c89fb44bcc903d63759808ac.jpg
