ArthurLimaMiranda/Projeto_FigurePicker/Vision_picker/yolov11s/dataset_balanced/test/images/yellow_cube115_png_jpg.rf.5259ddfc794b8cf1a431a8e1654c986c.jpg

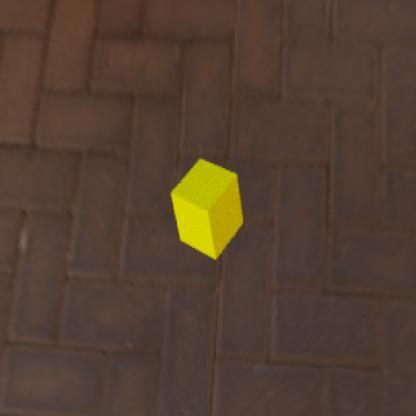
Vision_picker/yolov11s/dataset_balanced/test/images/yellow_cube115_png_jpg.rf.5259ddfc794b8cf1a431a8e1654c986c.jpg
