ArthurLimaMiranda/Projeto_FigurePicker/Vision_picker/yolov11s/dataset_balanced/test/images/yellow_cube119_png_jpg.rf.0bd66bd310a4e14bf9bf14ee5222787c.jpg

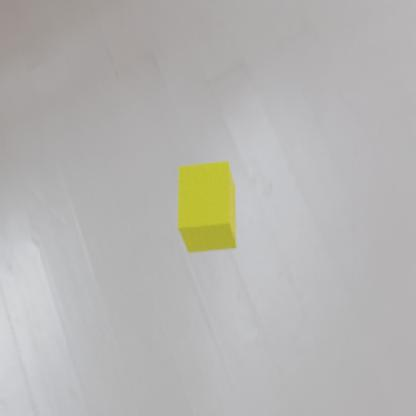
Vision_picker/yolov11s/dataset_balanced/test/images/yellow_cube119_png_jpg.rf.0bd66bd310a4e14bf9bf14ee5222787c.jpg
