ArthurLimaMiranda/Projeto_FigurePicker/Vision_picker/yolov11s/dataset_balanced/test/images/yellow_cube132_png_jpg.rf.850e8f18d03b1eb97e25869068882a4f.jpg

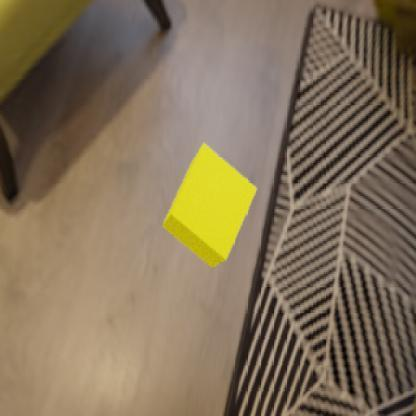
Vision_picker/yolov11s/dataset_balanced/test/images/yellow_cube132_png_jpg.rf.850e8f18d03b1eb97e25869068882a4f.jpg
