ArthurLimaMiranda/Projeto_FigurePicker/Vision_picker/yolov11s/dataset_balanced/test/images/yellow_cube135_png_jpg.rf.009c31b0f78e7369ba6ab09650c82188.jpg

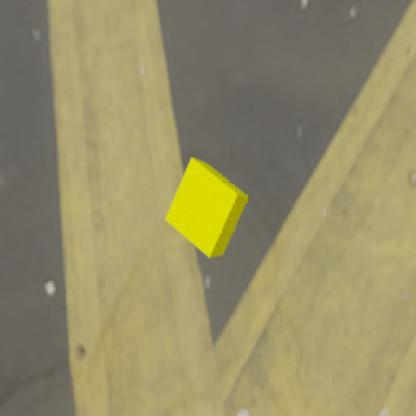
Vision_picker/yolov11s/dataset_balanced/test/images/yellow_cube135_png_jpg.rf.009c31b0f78e7369ba6ab09650c82188.jpg
