ArthurLimaMiranda/Projeto_FigurePicker/Vision_picker/yolov11s/dataset_balanced/test/images/yellow_cube140_png_jpg.rf.023b277b3b22217f810b3c1b5dbb430f.jpg

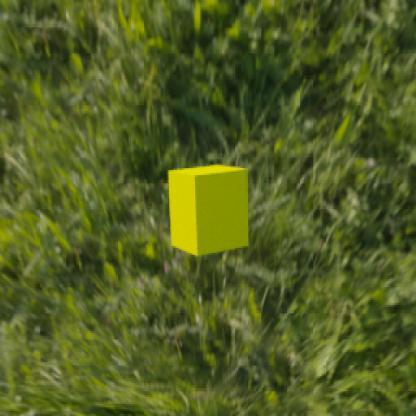
Vision_picker/yolov11s/dataset_balanced/test/images/yellow_cube140_png_jpg.rf.023b277b3b22217f810b3c1b5dbb430f.jpg
