ArthurLimaMiranda/Projeto_FigurePicker/Vision_picker/yolov11s/dataset_balanced/test/images/yellow_cube162_png_jpg.rf.069e72e5f454752c9e36902bbda47bd9.jpg

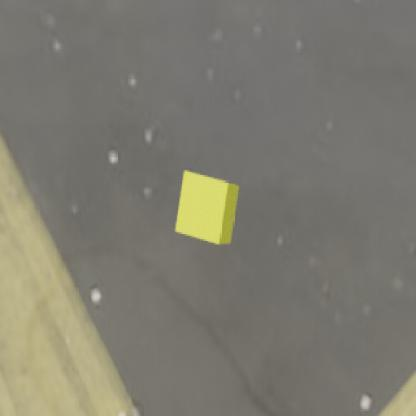
Vision_picker/yolov11s/dataset_balanced/test/images/yellow_cube162_png_jpg.rf.069e72e5f454752c9e36902bbda47bd9.jpg
