ArthurLimaMiranda/Projeto_FigurePicker/Vision_picker/yolov11s/dataset_balanced/test/images/yellow_cube167_png_jpg.rf.88d70bc7b6ee6ea210f34f0b1657bea4.jpg

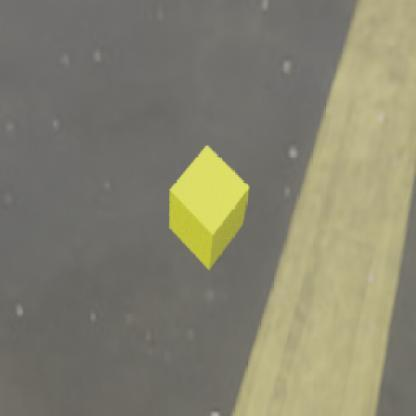
Vision_picker/yolov11s/dataset_balanced/test/images/yellow_cube167_png_jpg.rf.88d70bc7b6ee6ea210f34f0b1657bea4.jpg
