ArthurLimaMiranda/Projeto_FigurePicker/Vision_picker/yolov11s/dataset_balanced/test/images/yellow_cube168_png_jpg.rf.d0f31266af2161eb95295eddca04ba23.jpg

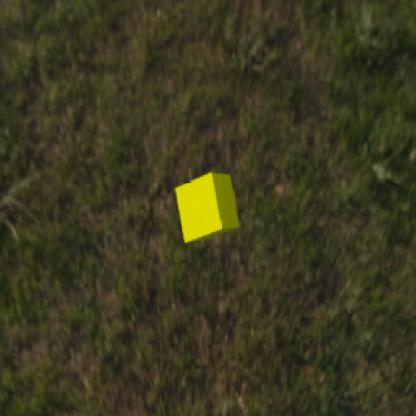
Vision_picker/yolov11s/dataset_balanced/test/images/yellow_cube168_png_jpg.rf.d0f31266af2161eb95295eddca04ba23.jpg
