ArthurLimaMiranda/Projeto_FigurePicker/Vision_picker/yolov11s/dataset_balanced/test/images/yellow_cube169_png_jpg.rf.f9ac7e3952c8e3c60673b94492728dd5.jpg

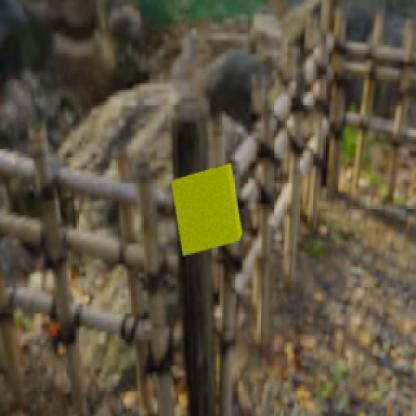
Vision_picker/yolov11s/dataset_balanced/test/images/yellow_cube169_png_jpg.rf.f9ac7e3952c8e3c60673b94492728dd5.jpg
