ArthurLimaMiranda/Projeto_FigurePicker/Vision_picker/yolov11s/dataset_balanced/test/images/yellow_cube171_png_jpg.rf.a1f7d73920e93c4e131f1bb76f532689.jpg

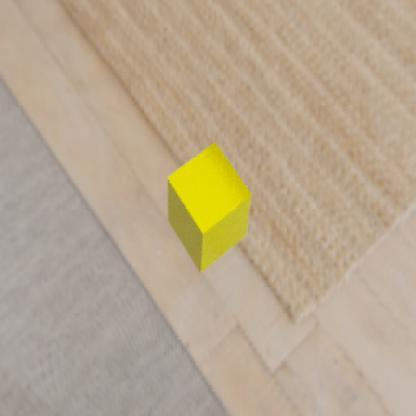
Vision_picker/yolov11s/dataset_balanced/test/images/yellow_cube171_png_jpg.rf.a1f7d73920e93c4e131f1bb76f532689.jpg
