ArthurLimaMiranda/Projeto_FigurePicker/Vision_picker/yolov11s/dataset_balanced/test/images/yellow_cube183_png_jpg.rf.292f5128d749c494d541f992a876b474.jpg

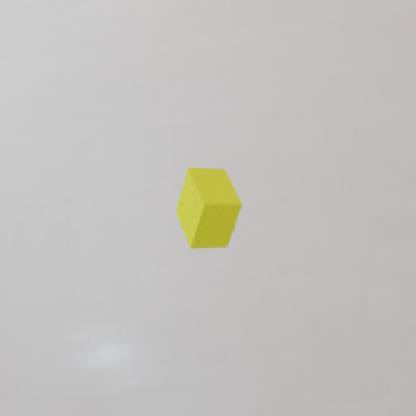
Vision_picker/yolov11s/dataset_balanced/test/images/yellow_cube183_png_jpg.rf.292f5128d749c494d541f992a876b474.jpg
