ArthurLimaMiranda/Projeto_FigurePicker/Vision_picker/yolov11s/dataset_balanced/test/images/yellow_cube187_png_jpg.rf.89d27a69ecc96027add2b8f595572698.jpg

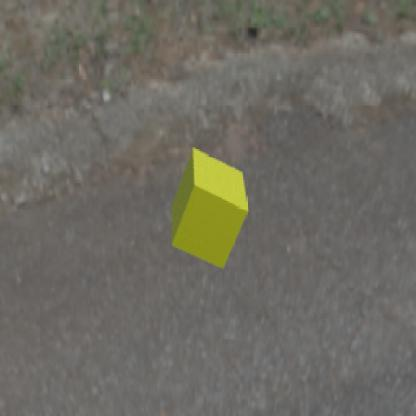
Vision_picker/yolov11s/dataset_balanced/test/images/yellow_cube187_png_jpg.rf.89d27a69ecc96027add2b8f595572698.jpg
