ArthurLimaMiranda/Projeto_FigurePicker/Vision_picker/yolov11s/dataset_balanced/test/images/yellow_cube202_png_jpg.rf.4e02b7699ad41902edc48b05b3738bd2.jpg

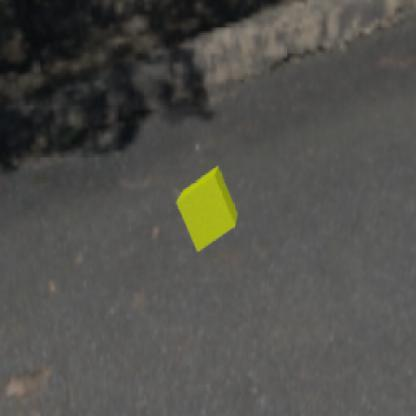
Vision_picker/yolov11s/dataset_balanced/test/images/yellow_cube202_png_jpg.rf.4e02b7699ad41902edc48b05b3738bd2.jpg
