ArthurLimaMiranda/Projeto_FigurePicker/Vision_picker/yolov11s/dataset_balanced/test/images/yellow_cube209_png_jpg.rf.61fc01d9a5684b1c2be21f2c76306c29.jpg

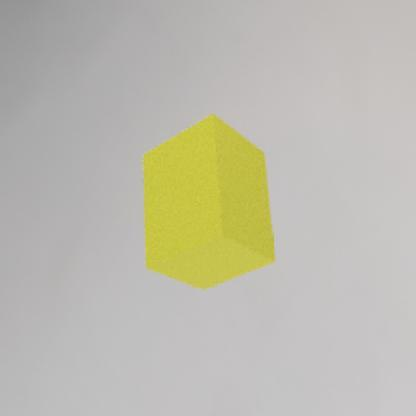
Vision_picker/yolov11s/dataset_balanced/test/images/yellow_cube209_png_jpg.rf.61fc01d9a5684b1c2be21f2c76306c29.jpg
