ArthurLimaMiranda/Projeto_FigurePicker/Vision_picker/yolov11s/dataset_balanced/test/images/yellow_cube226_png_jpg.rf.85c1d56b900f0e553f2f05852e8cd1e4.jpg

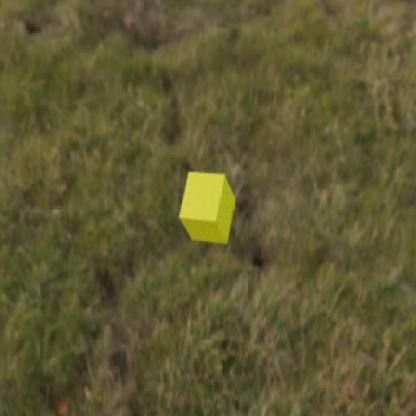
Vision_picker/yolov11s/dataset_balanced/test/images/yellow_cube226_png_jpg.rf.85c1d56b900f0e553f2f05852e8cd1e4.jpg
