ArthurLimaMiranda/Projeto_FigurePicker/Vision_picker/yolov11s/dataset_balanced/test/images/yellow_cube237_png_jpg.rf.3734e9d2cb4bf4e25800640c409b0455.jpg

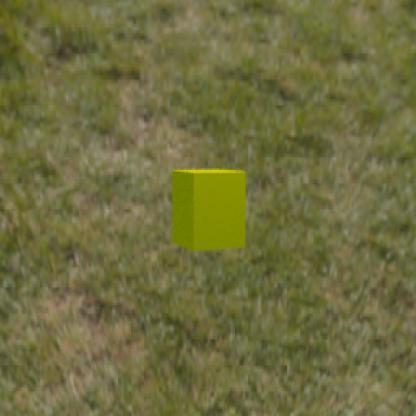
Vision_picker/yolov11s/dataset_balanced/test/images/yellow_cube237_png_jpg.rf.3734e9d2cb4bf4e25800640c409b0455.jpg
