ArthurLimaMiranda/Projeto_FigurePicker/Vision_picker/yolov11s/dataset_balanced/test/images/yellow_cube250_png_jpg.rf.ab07eb856c8a7f0934551a572788d945.jpg

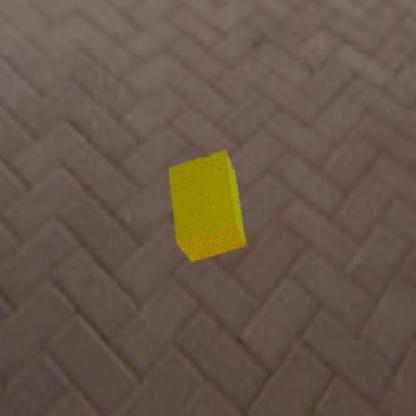
Vision_picker/yolov11s/dataset_balanced/test/images/yellow_cube250_png_jpg.rf.ab07eb856c8a7f0934551a572788d945.jpg
