ArthurLimaMiranda/Projeto_FigurePicker/Vision_picker/yolov11s/dataset_balanced/test/images/yellow_cube252_png_jpg.rf.ba966f387c0912438626318b1c90d729.jpg

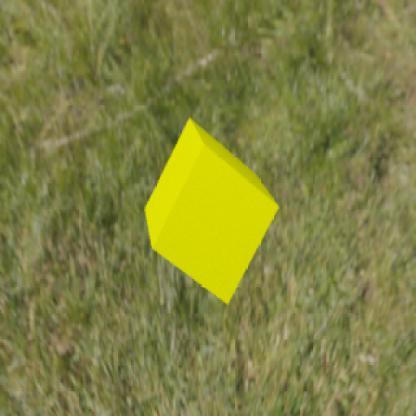
Vision_picker/yolov11s/dataset_balanced/test/images/yellow_cube252_png_jpg.rf.ba966f387c0912438626318b1c90d729.jpg
