ArthurLimaMiranda/Projeto_FigurePicker/Vision_picker/yolov11s/dataset_balanced/test/images/yellow_cube268_png_jpg.rf.b52f06d06c614de2ab3ecac7bbf11e4c.jpg

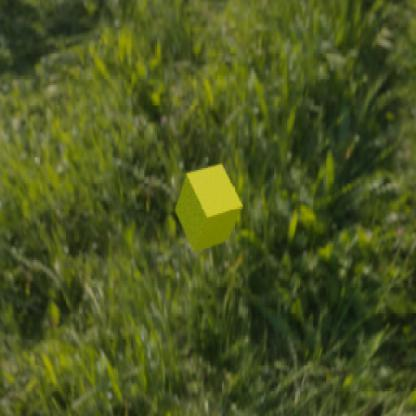
Vision_picker/yolov11s/dataset_balanced/test/images/yellow_cube268_png_jpg.rf.b52f06d06c614de2ab3ecac7bbf11e4c.jpg
