ArthurLimaMiranda/Projeto_FigurePicker/Vision_picker/yolov11s/dataset_balanced/test/images/yellow_cube384_png_jpg.rf.c91b976dd29e04c1bacd08a7fad185b3.jpg

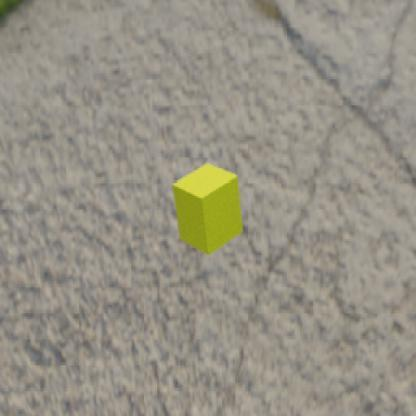
Vision_picker/yolov11s/dataset_balanced/test/images/yellow_cube384_png_jpg.rf.c91b976dd29e04c1bacd08a7fad185b3.jpg
