ArthurLimaMiranda/Projeto_FigurePicker/Vision_picker/yolov11s/dataset_balanced/test/images/yellow_cube387_png_jpg.rf.d9f2f596bce40a2c3899784447d64b47.jpg

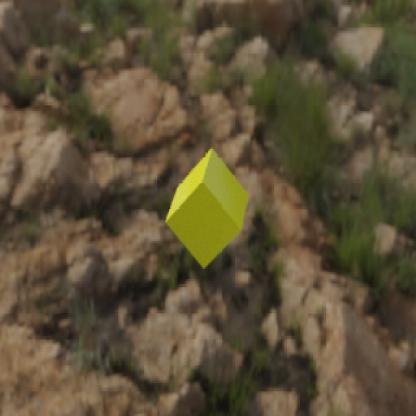
Vision_picker/yolov11s/dataset_balanced/test/images/yellow_cube387_png_jpg.rf.d9f2f596bce40a2c3899784447d64b47.jpg
