ArthurLimaMiranda/Projeto_FigurePicker/Vision_picker/yolov11s/dataset_balanced/test/images/yellow_cube392_png_jpg.rf.7e25d2ae0d126484c182e8059c004609.jpg

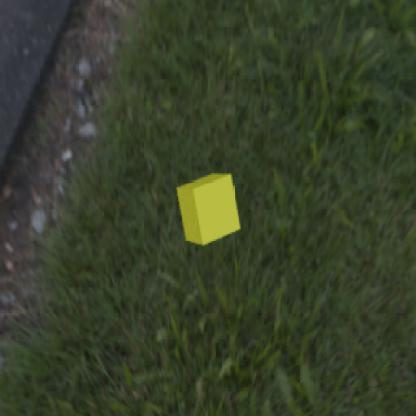
Vision_picker/yolov11s/dataset_balanced/test/images/yellow_cube392_png_jpg.rf.7e25d2ae0d126484c182e8059c004609.jpg
