ArthurLimaMiranda/Projeto_FigurePicker/Vision_picker/yolov11s/dataset_balanced/test/images/yellow_cube399_png_jpg.rf.83b1860ffd69ca5a10693680e8b6d452.jpg

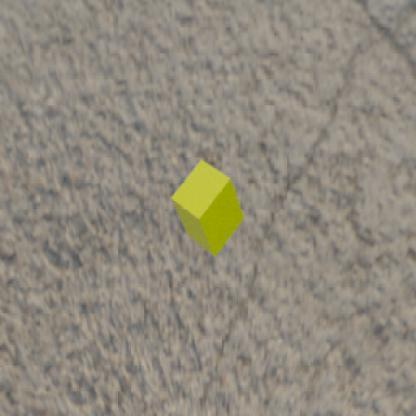
Vision_picker/yolov11s/dataset_balanced/test/images/yellow_cube399_png_jpg.rf.83b1860ffd69ca5a10693680e8b6d452.jpg
